deemonoise/D-TRK/docs/plans/2026-10-09-clamps-v2.md

# Клэмпы v2 — план реализации

> **For Claude:** REQUIRED SUB-SKILL: Use superpowers:executing-plans to implement this plan task-by-task.

**Goal:** 4 лапки, прижимающие модуль за угловые бобышки, на существующих стойках верха.

**Architecture:** Новый `module clamp2(dx, dy)` в `enclosure/case.scad`: hull винта и бобышки,
площадка `foam_t` и штырёк в отверстие бобышки. `part = "clamp2"` — 4 лапки на столе,
assembly показывает лапки. Коммиты не делать (правило пользователя).

**Tech Stack:** OpenSCAD 2021.01 (`/Applications/OpenSCAD-2021.01.app/Contents/MacOS/OpenSCAD`).

---

### Task 1: Переменные бобышек

**Files:** Modify: `enclosure/case.scad` (блок «Замерить перед печатью», «Производные»)

Добавить после `clamp_dx`:
```
// Бобышки на задней стороне модуля (клэмпы v2)
boss_x0 = 6.52;    // центр от левого края модуля
boss_x1 = 10.34;   // центр от правого края (сторона Type-C модуля)
boss_y  = 4.3;     // центр от длинных краёв
boss_d  = 6.0;     // наружный диаметр (не замерен)
boss_hole = 2.5;   // отверстие (не замерено)
boss_flip = false; // true — Type-C модуля слева
pin_d = 2.0; pin_h = 1.5;   // штырёк лапки в отверстие бобышки
```
В «Производные» после `clamp_ys`:
```
boss_xs = [mod_x0 + mod_clr + (boss_flip ? boss_x1 : boss_x0),
           mod_x1 - mod_clr - (boss_flip ? boss_x0 : boss_x1)];
boss_ys = [mod_y0 + mod_clr + boss_y, mod_y1 - mod_clr - boss_y];
```

### Task 2: module clamp2 и part

**Files:** Modify: `enclosure/case.scad` (после `module clamp`, assembly, выбор part)

```
// ---------- Лапка v2: винт на стойке, площадка со штырьком на бобышке ----------
// (dx, dy) — смещение центра бобышки от винта
module clamp2(dx, dy) {
    difference() {
        union() {
            hull() {
                cylinder(r = post_r, h = clamp_t);
                translate([dx, dy, 0]) cylinder(d = boss_d, h = clamp_t);
            }
            translate([dx, dy, clamp_t - 0.01]) {
                cylinder(d = boss_d, h = foam_t + 0.01);
                cylinder(d = pin_d, h = foam_t + pin_h + 0.01);
            }
        }
        translate([0, 0, -1]) cylinder(d = screw_d, h = clamp_t + 2);
    }
}
function clamp2_off(i, j) = [boss_xs[i] - clamp_xs[i], boss_ys[j] - clamp_ys[j]];
```
Assembly: заменить строку старых планок на
```
for (i = [0, 1], j = [0, 1]) color("orange")
    translate([clamp_xs[i], clamp_ys[j], clamp_zt - clamp_t])
        clamp2(clamp2_off(i, j)[0], clamp2_off(i, j)[1]);
```
Выбор part: `else if (part == "clamp2") for (i = [0, 1], j = [0, 1]) translate([i*25, j*30, 0]) clamp2(clamp2_off(i, j)[0], clamp2_off(i, j)[1]);`
Шапку файла дополнить `"clamp2"`.

### Task 3: Проверка рендера

Run: `$OS -o /tmp/a.stl -D 'part="clamp2"' case.scad` и `$OS -o /tmp/b.png -D 'part="assembly"' case.scad`
Expected: без WARNING/ERROR, 4 лапки, площадки упираются в низ модуля, лапки не задевают стенки и аккумулятор.
Проверить зазор: `intersection(){ лапки без штырька; модуль }` пусто.

### Task 4: STL и README

- `$OS -o stl/clamp2.stl -D 'part="clamp2"' case.scad`
- `enclosure/README.md`, `README_ru.md`: таблица печати `stl/clamp2.stl` — 1 стол (4 лапки), старые планки как v1;
  крепёж — скотч не нужен для v2; шаг сборки — штырьки в отверстия бобышек; команда рендера; переменные `boss_*`.
