deemonoise/D-TRK/docs/plans/2026-10-06-roadmap.md

# Roadmap: 16 tracks, drum track, song & live, sound, mixer & render

Agreed 2026-10-06. Five blocks, each with its own design + plan, executed in separate sessions in
this order. Every block bumps the project file format (new chunks; older files load with defaults;
files written by a newer block do not open on older firmware).

| # | Block | Design | Plan | Depends on | Status |
|---|---|---|---|---|---|
| 1 | 16 tracks (A/B halves follow the cursor, 8 buttons on the visible half, undo depth 8) | `2026-10-06-16-tracks-design.md` | `2026-10-06-16-tracks.md` | SYNTH / wavetable work landed (`model.h`) | ✅ done 2026-10-06 (checked on the device) |
| 2 | Drum track: KIT instrument (8 lanes, each its own sample by default, optionally an instrument ref), lane mask in `Step::vel`, x-ox views, `ACC` fx | `2026-10-06-kit-drum-track-design.md` | `2026-10-06-kit-drum-track.md` | 1 | ✅ done 2026-10-06 (checked on the device) |
| 3 | Song + live: chain transpose / repeat / scene (`CHN2`), per-track length (`TLEN`), fill (`FIL` / `NFL`, Shift+Play), mute scenes (`SCNS`), live record, punch-in fx (PERF) | `2026-10-06-song-live-design.md` | `2026-10-06-song-live.md` | 1, 2 (drum tracks skip transpose) || ✅ done 2026-10-06 (checked on the device) |
| 4 | Sound: drive (`DRV`), reverb send (`RVB`), master compressor + sidechain, `ARM` arp modes, ARP over CHD, velocity → cutoff / decay | `2026-10-06-sound-fx-design.md` | `2026-10-06-sound-fx.md` | SYNTH / wavetable work landed; 1–3 for track numbers || ✅ done 2026-10-06 (checked on the device) |
| 5 | MIXER view (now its own MIX tab) + offline render: Render WAV (FILE), Resample track / pattern into a project sample (GRID) | `2026-10-06-mixer-render-design.md` | `2026-10-06-mixer-render.md` | 1–4 (render includes delay / reverb / comp) || ✅ done 2026-10-06 (checked on the device) |

Block 1 landed 2026-10-06 and was checked on the device.

Block 2 progress 2026-10-06: tasks 1–5 (model, `ACC`, `KITS` chunk, rename, `expandDrum`) landed, 733
native tests, wt32 builds. Follow-up found in review (resolved with tasks 6–11, see below): the used-sample scan in
`lib/core/src/sample_set.cpp` (`UsedKeys`, ~line 235) and any other "is this sample referenced" site
(bank eviction, project save WAV list, FILE → SAMPLES "in use") must also count `kit[k].sample` of KIT
instruments — do it with task 6 or as its own step before task 11. Also for task 10: add `Kit` cases to
`preset_paths.cpp` `presetTypeName` / `presetRoot` and a `static_assert` on `kTypeNames[]` in
`inst_screen.cpp`.

Block 2, tasks 6–11 (2026-10-06): synth lanes (`Voice::lane` / `laneInst`, `instrOf`, `allocVoice(...,
polyMax)`), Euclid lane, Transpose skips drum tracks, MIDI import onto lanes, GRID mask / lane pad /
track buttons, Euclid dialog `Lane`, INST KIT pages (MAIN + LANES), no KIT presets (`presetTypeHas`),
import dialog `T5*`, README + manual. The used-sample follow-up: `UsedKeys` works from the project
sample list, so lanes were already covered; FILE → SAMPLES Delete now asks through
`projSampleUser`, which counts KIT sampler lanes. 747 native tests pass (run with g++ and a Unity
shim: the PlatformIO registry was not reachable in that session); the UI was type-checked against
host stubs only — `pio run -e wt32` still to run. `Voice` grew by `sizeof(Instrument)` (358 B on
the host), ~5.7 KB for 16 voices: check the boot heap log.

Block 3 (2026-10-06): chain items with transpose / passes / scene (`CHN2`), per-track length
(`TLEN`, `Pattern::trackLen`), mute scenes (`SCNS`, BANK tiles), fill (`CND FIL / NFL`, Shift + Play
held), REC and PERF on the track buttons (`PlayRelease` / `TrackRelease` events, `Cmd::Fill / PerfOn /
PerfOff`, `Status::fill / stepT / stepUs`). 772 native tests pass (g++ + a Unity shim, the PlatformIO
registry still unreachable); UI, engine and trackio type-checked against host stubs only. Choices
beyond the plan: an out-of-range scene in `CHN2` loads as none; deleting the playing chain item
advances at the pass end; REC on a drum track toggles lanes; PERF Fade on a MIDI track halves the
velocity; tapping a track name in REC selects the track instead of muting. To verify on the device:
`pio run -e wt32`, button release timing (fill, PERF), REC landing on the right step, BANK row fields
and scene tiles, the GRID loop line of a short track.

Block 4 (2026-10-06): `Drive` (tanh table, per voice before the filter, lock `DRV`, LFO `DRIVE`),
`Reverb` (Freeverb-lite, 23 KB float buffer in PSRAM, send per instrument, lock `RVB`, idles once its
tail dies out), `Compressor` (master, sidechain bus of `scTrack`), `ARM` modes / rate and ARP + CHD
(`kSynthArpChord`, chord computed at note-on from the played note), velocity -> cutoff / DECAY.
Formats: FMIN bytes 10..13, AUDI 13 bytes, presets v4. 807 native tests pass (g++ + Unity shim);
UI type-checked against host stubs. Choices beyond the plan: ARM DOWN starts from the top note;
makeup gain = threshold drop / 4 (design text) not / 2 (plan code); KIT sampler lanes take the kit's
Rvb send; KIT MAIN page shows Rvb send. To do on the device: `pio run -e wt32`, the CPU bench
(`pio run -e wt32-fxbench`, numbers into the design doc), listening.

Block 5 (2026-10-06): `mt::OfflineRender` (own sequencer on a virtual block clock, live synth,
analytic length, only note-offs after the end, deterministic seed), `Sequencer::setTrackMask`,
`storage::renderWav` / `resample`, `audio::Paused` / `liveSynth`, `audio::cacheWrite` (bank write from
generated data, `finishImport` shared with WAV import), FILE `Render WAV...`, GRID `Resample track /
pattern`, TRACK MIXER view (MAIN = master volume, gone from PROJ), hold a track button + turn =
volume. 823 native tests pass (g++ + Unity shim); UI, render_io, bank, storage type-checked against
host stubs. Choices beyond the plan: renders go to `/samples/render/<project>_P01.wav` / `_SONG.wav`
(Save cleans unknown WAVs out of the project folder, and the Wi-Fi page lists /samples); after the
end only note-offs / releases pass (not controls or synth fx of the next pass); the render guard also
restores track mutes (chain scenes); cancel = long encoder press or Play; MIXER Shift + turn runs
strips 1-8, MAIN, 9-16. Block 4 still waits for its device check (CPU bench numbers).

After the blocks (2026-10-06, from device feedback):
- Step arp `ARS` (fx, INT and MIDI): the sequencer plays the arp as real notes on the following
  steps without a note, every 1..8 steps, ARM orders, 1..4 octaves (`U12` = up, every step, 2
  octaves); notes = CHD chord, else ARP 0/x/y, else the root over at least 2 octaves; stops on a
  note step, OFF, a pattern change, stop. The fast synth ARP / ARM stay as they were.
- Fx command order grouped by meaning in GRID (`fxNextCmd` table; the enum / file format is
  unchanged): notes and arp, timing, chance, pitch and level, sound locks, sample, sends, MIDI only.
- MIDI import: no second project copy (the confirmation runs `importPlan`, the commit imports
  straight into the live project under the lock); the note buffer follows the file size. Fixes NO
  MEMORY on confirm.
- SD: WAV data clamped to the file size (cut files no longer read past the end); `hw::sdRecover`
  remounts only when the card stops answering; `sdBegin` retries with a bus reset. Fixes the card
  being lost until reboot after a sample import / preview error.
- MIXER became the MIX tab of the bottom bar (seven tabs); the Shift + tap / Shift + click / menu
  toggles are gone.

Feature batch (2026-10-06, after the review fixes): restart log + firmware version (crashlog.txt,
PROJ -> SYS), stem export (Render WAV -> STEMS), autosave slot (.auto) + Restore + safe boot (Shift at
power-on), project templates (FILE -> New, /templates), CND PRE / NEI, RAT ramps, groove templates per
pattern + humanize per track (GROV chunk), BIT / SRR lo-fi locks, master DJ filter (AUDI byte 13), PERF
buttons per project (PROJ -> PERF, PRFM chunk), 4 LFOs per instrument with tempo sync (LFOX chunk,
presets v5), FILE sections as page tabs, Wi-Fi page with tabs and scrolling lists.
GRID Fill (Polyend-style) done: `lib/core/src/fill.{h,cpp}` (EVERY N / EUCLID / RANDOM %; NOTE, VEL or an FX slot; CONST / RAMP / RANDOM, notes in the scale; OVERWRITE / EMPTY / NOTES ONLY), `src/ui/fill_dialog` replaces the Euclid dialog (selection or the track up to its length). Euclid core keeps only `euclid()`.

Status 2026-10-07: every block is ✅ — built (`pio run -e wt32`), flashed and checked on the device,
including the feature batch, GRID Fill, the CPU work (voice control in IRAM, math caches, reverb buffer
in internal RAM: ~31 % instead of ~60 % on the heaviest test project), the CPU profile (PROJ -> SYS),
the MIX tab (scope, master on the encoder, A / B, level meters while MIX is shown), page tabs like
FILE on TRACK / PROJ / INST, Bit crush / Downsample in the instrument, the 145-preset factory library
and the SYNTH level fix. Nothing open on this roadmap.

Rules for every session: no commits unless asked; run `pio test -e native` and `pio run -e wt32`
at the end of each task; do not stop for hardware checks — finish the plan, then summarize what to
verify on the device.

Dropped / deferred ideas (see the discussion of 2026-10-06): more than 16 patterns (chain transpose
covers it), song loop points, USB-MIDI device, SMF export, LSDJ-style tables, pan (mono output).
