deemonoise/D-TRK/docs/plans/2026-10-06-16-tracks.md

# 16 Tracks Implementation Plan

> **For Claude:** REQUIRED SUB-SKILL: Use superpowers:executing-plans to implement this plan task-by-task.

**Goal:** Raise the track count from 8 to 16; old project files still load; the GRID overview and the 8 track buttons work on the half (1–8 / 9–16) that holds the cursor.

**Architecture:** `kTracks` becomes 16 and everything sized by it follows. The PATN reader infers the file's track count from the chunk size instead of assuming `kTracks`. The "half" is not state: it is `curTrack / 8`, so moving the cursor is the only way to switch it. Activity / LED masks widen to 16 bits in the core and the engine; the LED mask for the 8 physical LEDs is cut out of the half that holds the selected track.

**Tech Stack:** C++17, PlatformIO (`pio test -e native` for the core, `pio run -e wt32` for the firmware), Unity tests. Design: `docs/plans/2026-10-06-16-tracks-design.md`.

**Rules for this project:** no commits (the user commits); do not stop for hardware checks — finish all tasks, then summarize. Another agent is working in `lib/core/src/synth_syn*`, `wt_*`, `inst_screen.cpp` (SYNTH / wavetable): do not touch those files; if `model.h` has merge noise, keep both changes.

---

### Task 1: `kTracks = 16` in the model

**Files:**
- Modify: `lib/core/src/model.h:6`
- Modify: `src/ui/grid_screen.h:93`
- Modify: `src/audio/audio.cpp:319-321`
- Test: `test/test_model/test_main.cpp`

**Step 1: Write the failing test**

Append to `test/test_model/test_main.cpp` (register with `RUN_TEST` next to the other model tests):

```cpp
void test_sixteen_tracks_defaults() {
  Project p;
  TEST_ASSERT_EQUAL(16, kTracks);
  for (int i = 0; i < kTracks; ++i) {
    TEST_ASSERT_EQUAL(i, p.tracks[i].channel);
    TEST_ASSERT_EQUAL(i, p.tracks[i].instr);
    char nm[9];
    snprintf(nm, sizeof(nm), "TRK%d", i + 1);
    TEST_ASSERT_EQUAL_STRING(nm, p.tracks[i].name);
  }
  TEST_ASSERT_EQUAL(16, kInstruments);  // one instrument per track
}
```

**Step 2: Run it**

Run: `pio test -e native -f test_model`
Expected: FAIL (`Expected 16 Was 8`).

**Step 3: Implement**

`lib/core/src/model.h:6`: `constexpr int kTracks = 16;`

`src/ui/grid_screen.h:93` — the initializer lists 8 values; make it independent of the count:

```cpp
  uint8_t lastNote_[mt::kTracks];  // set to 60 in the constructor
```

and in the constructor (`grid_screen.h:13`):

```cpp
  explicit GridScreen(App& app) : app_(app) { for (uint8_t& n : lastNote_) n = 60; }
```

`src/audio/audio.cpp:319-321` (`AUDIO_BENCH_DRUM` only): the table has 8 entries for `kTracks` slots. Size it by its own length and wrap:

```cpp
  static const DrumMachine kMachines[] = {DrumMachine::Bd8, DrumMachine::Sd8, DrumMachine::Hh8,
                                          DrumMachine::Cy9, DrumMachine::Cp8, DrumMachine::Cb8,
                                          DrumMachine::Tom9, DrumMachine::Hh9};
  constexpr int kBenchTracks = 8;  // instruments kBenchDrumInstr..15
  for (int t = 0; t < kBenchTracks; ++t) {
    ...
    mt::drumSetMachine(d, static_cast<uint8_t>(kMachines[t % 8]));
```

(`benchDrumHits` likewise loops `kBenchTracks`; instruments 8..15 are only 8.)

**Step 4: Run the model test and the whole native suite**

Run: `pio test -e native -f test_model` → PASS.
Run: `pio test -e native` → note every failing test: they are the 8-track assumptions fixed in Tasks 2–4. Do not fix them blindly here.

---

### Task 2: PATN reader infers the file's track count

**Files:**
- Modify: `lib/core/src/project_io.cpp:234-262` (`readPatn`)
- Test: `test/test_project_io/test_main.cpp`

**Step 1: Write the failing tests**

In `test/test_project_io/test_main.cpp` the helper `patn()` (line 451) writes `kTracks` tracks of 6-byte steps. Give it the track count and the step size:

```cpp
// A PATN body: `tracks` tracks of `stepBytes`-byte steps (6 = the 2-slot format, 14 = current).
static std::vector<uint8_t> patn(uint8_t idx, uint8_t len, int extraBytes = 0, int tracks = kTracks,
                                 int stepBytes = 6) {
  std::vector<uint8_t> p = {idx, len, static_cast<uint8_t>(Resolution::Eighth), 60};
  for (int t = 0; t < tracks; ++t)
    for (int s = 0; s < len; ++s) {
      std::vector<uint8_t> st(stepBytes, 0);
      st[0] = static_cast<uint8_t>((t + s) % 128);
      st[1] = 100;
      p.insert(p.end(), st.begin(), st.end());
    }
  if (extraBytes > 0) p.resize(p.size() + extraBytes, 0);
  if (extraBytes < 0) p.resize(p.size() + extraBytes);
  return p;
}
```

Add tests:

```cpp
// Files from the 8-track firmware: tracks 1-8 load, 9-16 stay clear. Both step formats.
void test_patn_eight_tracks_loads() {
  for (int stepBytes : {6, 14}) {
    std::vector<uint8_t> f = fileHeader();
    putChunk(f, "PATN", patn(3, 16, 0, 8, stepBytes));
    finish(f);
    TEST_ASSERT_EQUAL(static_cast<int>(LoadErr::Ok), static_cast<int>(loadBytes(f)));
    const Pattern& pt = b.patterns[3];
    TEST_ASSERT_EQUAL(16, pt.length);
    TEST_ASSERT_EQUAL((7 + 15) % 128, pt.steps[7][15].note);
    for (int t = 8; t < kTracks; ++t)
      for (int s = 0; s < 16; ++s) TEST_ASSERT_TRUE(pt.steps[t][s].isEmpty());
  }
}

void test_patn_sixteen_tracks_round_trip() {
  a.reset();
  a.patterns[5].length = 24;
  a.patterns[5].steps[15][23].note = 71;
  a.patterns[5].steps[8][0].fx[5] = {Fx::DLY, 99};
  VecSink out;
  TEST_ASSERT_TRUE(saveProject(a, out));
  VecSource in(out.data);
  TEST_ASSERT_EQUAL(static_cast<int>(LoadErr::Ok), static_cast<int>(loadProject(in, b)));
  TEST_ASSERT_EQUAL(71, b.patterns[5].steps[15][23].note);
  TEST_ASSERT_EQUAL(static_cast<int>(Fx::DLY), static_cast<int>(b.patterns[5].steps[8][0].fx[5].cmd));
  TEST_ASSERT_EQUAL(99, b.patterns[5].steps[8][0].fx[5].val);
}
```

(`VecSink` / `VecSource`: use whatever the file's `test_round_trip_full_project` uses — copy its pattern.)

`test_patn_size_mismatch` must still pass: an 8-track 6-byte body ± 1 byte and + 6 bytes match none of the four (tracks, step) combinations. Keep `test_trks_count_not_eight` as is: the `trks(10, 10)` case now loads 10 tracks (count ≤ kTracks); update its assertions: `b.tracks[9].name == "K9"`, and tracks 10–15 keep the defaults.

**Step 2: Run them**

Run: `pio test -e native -f test_project_io`
Expected: `test_patn_eight_tracks_loads` FAILS (`BadValue`), the round trip passes already.

**Step 3: Implement**

Replace the step-size inference in `readPatn` (`project_io.cpp:239-246`) and the fill loop:

```cpp
  const int len = h[1];
  // Track count and step size from the body size: 16 or 8 tracks (files of the 8-track firmware)
  // x 14-byte (6 slots) or 6-byte (2 slots, older) steps. The four products differ for any length.
  const uint32_t body = size - kPatHeader;
  int tracks = 0;
  uint32_t stepBytes = 0;
  for (int tr : {kTracks, 8})
    for (uint32_t sb : {static_cast<uint32_t>(sizeof(Step)), kOldStepBytes})
      if (!stepBytes && len && body == static_cast<uint32_t>(tr) * len * sb) {
        tracks = tr;
        stepBytes = sb;
      }
  if (!stepBytes && body != 0) return LoadErr::BadValue;
```

and `for (int t = 0; t < tracks; ++t)` in the step loop (`pt.clear()` already zeroes the rest). Keep the `len == 0` behaviour: `body == 0` → an empty pattern of `kMinSteps`.

**Step 4: Run**

Run: `pio test -e native -f test_project_io` → all PASS.

---

### Task 3: 16-bit activity for the LEDs, half-aware LED mask

**Files:**
- Modify: `lib/core/src/sequencer.h:86-91,182`, `lib/core/src/sequencer.cpp:624`
- Modify: `src/engine/engine.h:39`, `src/engine/engine.cpp:31,72-74,134`
- Modify: `lib/core/src/track_leds.h`
- Modify: `src/ui/app.cpp:206-214`, `src/ui/app.h:133` (unchanged size, keep)
- Test: `test/test_track_leds/test_main.cpp`

**Step 1: Write the failing test**

```cpp
// 16 tracks, 8 LEDs: the LEDs show the half (tracks 1-8 or 9-16) that holds the selected track.
void test_half_mask_follows_selected() {
  // selected 11 (half B, LED 3), track 9 flashing (LED 1), track 2 flashing (half A, hidden)
  TEST_ASSERT_EQUAL_HEX8((1 << 3) | (1 << 1), trackLedMaskHalf(11, (1u << 9) | (1u << 2)));
  // selected 2 (half A): track 9 hidden, track 2 flashing goes dark
  TEST_ASSERT_EQUAL_HEX8(0, trackLedMaskHalf(2, (1u << 9) | (1u << 2)));
  TEST_ASSERT_EQUAL_HEX8(1 << 7, trackLedMaskHalf(15, 0));
  TEST_ASSERT_EQUAL_HEX8(0, trackLedMaskHalf(-1, 1u << 9));  // nothing selected: half A
}
```

Register it in `main()`.

**Step 2: Run** `pio test -e native -f test_track_leds` → FAIL (no `trackLedMaskHalf`).

**Step 3: Implement**

`track_leds.h`, after `trackLedMask`:

```cpp
// 16 tracks on 8 LEDs: the half (tracks 0-7 or 8-15) holding the selected track; flash bit = track.
inline uint8_t trackLedMaskHalf(int selected, uint16_t flash) {
  const int half = selected >= 8 && selected < 16 ? 1 : 0;
  const uint8_t f = static_cast<uint8_t>(flash >> (half * 8));
  return trackLedMask(selected >= 0 ? selected - half * 8 : -1, f);
}
```

Widen the activity path to `uint16_t`:

- `sequencer.h`: `uint16_t takeActivity() { const uint16_t a = activity_; ... }`, `uint16_t activity_ = 0;`
- `sequencer.cpp:624`: `activity_ |= static_cast<uint16_t>(1u << e.track);`
- `engine.cpp:31`: `std::atomic<uint16_t> activity{0};`; line 72: `const uint16_t act = ...`; line 134 and `engine.h:39`: `uint16_t takeActivity()`.
- `app.cpp` `updateLeds`:

```cpp
void App::updateLeds(uint32_t now) {
  const uint16_t act = engine::takeActivity();
  uint16_t flash = 0;
  for (int i = 0; i < mt::kTracks; ++i) {
    if (act & (1u << i)) flashUntil_[i] = now + kFlashMs;
    if (static_cast<int32_t>(flashUntil_[i] - now) > 0) flash |= static_cast<uint16_t>(1u << i);
  }
  hw::trackLeds(mt::trackLedMaskHalf(curTrack_, flash));
}
```

**Step 4: Run** `pio test -e native -f test_track_leds` → PASS. `pio test -e native -f test_sequencer` → PASS (activity type only).

---

### Task 4: Core tests at the new bounds (edit ops, Euclid, sequencer, MIDI import)

**Files:**
- Modify: `lib/core/src/midi_import.h:11` (comment `0..7` → `0..kTracks-1`), `lib/core/src/edit_ops.h:20` (comment)
- Test: `test/test_edit/test_main.cpp`, `test/test_euclid/test_main.cpp`, `test/test_sequencer/test_main.cpp`, `test/test_import/test_main.cpp`

**Step 1: Add tests** (copy the style of the neighbouring tests in each file; names below):

- `test_edit`: `test_paste_clipped_at_track_16` — a 3-track clipboard pasted at track 14 writes tracks 14, 15 and drops the third; `test_selection_spans_halves` — `Sel` from track 5 to 10 (both orders) normalizes to t0 = 5, t1 = 10 and `clearSel` clears exactly those tracks.
- `test_euclid`: `test_euclid_track_15` — apply to track 15 with hits 4 / steps 16, four notes on that track, track 14 untouched.
- `test_sequencer`: `test_track_15_plays` — a note on track 15 at step 0 produces a NoteOn on channel `tracks[15].channel` (MIDI out) and `takeActivity()` has bit 15.
- `test_import`: `test_twelve_channels_to_twelve_tracks` — an SMF with notes on channels 1–12 (one source each) imported with the default map lands on tracks 0–11; track 11 holds the channel-12 note.

**Step 2: Run** `pio test -e native` → the new tests FAIL only if a bound is still 8 somewhere; expected: PASS straight away for edit / euclid / sequencer (they are `kTracks`-bounded), PASS for import.

If a test fails, the failing spot is a literal 8 — fix it in the core file, not the test.

**Step 3: Run the whole suite** `pio test -e native` → every test PASS.

---

### Task 5: GRID overview shows the cursor's half

**Files:**
- Modify: `src/ui/grid_screen.h` (add `half()`, `kOverviewTracks`)
- Modify: `src/ui/grid_screen.cpp:273-300` (`trackKey`, `hit`), `:336-345` (name tap), `:608-656` (`drawOverview`)

**Step 1: Helpers** in `grid_screen.h`, private:

```cpp
  static constexpr int kOverviewTracks = 8;                     // columns per half
  int half() const { return track() / kOverviewTracks; }         // 0 = tracks 1-8, 1 = 9-16
  int firstTrack() const { return half() * kOverviewTracks; }
```

**Step 2: `drawOverview`** — both loops over tracks become columns:

```cpp
  for (int col = 0; col < kOverviewTracks; ++col) {
    const int tr = firstTrack() + col;
    const mt::TrackCfg& t = p.tracks[tr];
    s.setTextColor(t.solo ? kCursor : (p.trackAudible(tr) ? kText : kDim));
    s.drawString(t.name, kNumW + col * kColW + 4, gridY - kNamesH);
  }
```

and in the row loop `for (int col ...) { const int tr = firstTrack() + col; const int x = kNumW + col * kColW; ... }` — every `pt.steps[tr]`, `p.tracks[tr]`, `selected(tr, step)`, `tr == track()` keeps the absolute `tr`; only `x` uses `col`.

Half indicator: in the step-number column header (top-left, `x = 2`, where Detail prints `T%d`) draw `"A"` or `"B"` in `kDim` when `!detail_`:

```cpp
  s.setTextColor(kDim);
  s.drawString(half() ? "9-16" : "1-8", 2, gridY - kNamesH);
```

(`kNumW` = 32 px: "1-8" / "9-16" fit in the default 6-px font; check on the device, fall back to "A" / "B" if not.)

**Step 3: `hit`** (overview branch):

```cpp
  if (!detail_) {
    const int col = (x - kNumW) / kColW;
    if (col >= kOverviewTracks) return false;
    tr = firstTrack() + col;
    field = kNote;
    return true;
  }
```

**Step 4: Name tap** (`:339-340`):

```cpp
    const int col = (ev.x - kNumW) / kColW;
    if (!detail_ && col >= kOverviewTracks) return;
    const int tr = detail_ ? track() : firstTrack() + col;
```

**Step 5: `trackKey`** — button N selects track N of the visible half; note entry keeps the button index:

```cpp
  if (shift) return false;
  app_.setCurTrack(firstTrack() + n);
```

(`enterDegree(n, shift)` above it stays: degrees are button numbers.)

**Step 6: `moveTrack` / `moveField`** need no change: `setCurTrack` wraps at 16, `half()` follows. `cursorMoved()` already requests a redraw.

**Step 7: Build** `pio run -e wt32` → compiles.

---

### Task 6: App maps the 8 buttons onto the visible half

**Files:**
- Modify: `src/ui/app.cpp:188-204` (`trackKey`)

**Step 1: Implement**

```cpp
// Button n (0-7) addresses track n of the half holding the cursor (1-8 or 9-16). Grid takes
// selection and note entry, the sample editor plays slices (button index); Shift + N mutes on
// every other screen too.
void App::trackKey(int n, bool shift) {
  if (n < 0 || n >= 8) return;
  const int track = (curTrack_ / 8) * 8 + n;
  if (tab_ == Tab::Grid && grid_.trackKey(n, shift)) return;
  if (tab_ == Tab::Inst && inst_.trackKey(n, shift)) return;
  if (!shift) {
    setCurTrack(track);
    return;
  }
  mt::TrackCfg& t = p_->tracks[track];
  ... (mute toggle as now, toast "TRACK %d" with track + 1)
```

**Step 2: Build** `pio run -e wt32` → compiles.

---

### Task 7: Undo depth and PSRAM budget

**Files:**
- Modify: `lib/core/src/undo.h:10`
- Check: `src/main.cpp`, `src/ui/app.cpp:17-19`

**Step 1:** `static constexpr int kDepth = 8;` (8 x 28 KB ≈ 230 KB; the project ≈ 460 KB).

**Step 2:** Make sure the boot log prints the free PSRAM after the project and undo buffers are allocated. If `main.cpp` does not log it, add after the undo allocation:

```cpp
  Serial.printf("psram free %u KB\n", heap_caps_get_free_size(MALLOC_CAP_SPIRAM) / 1024);
```

**Step 3:** `pio run -e wt32` → compiles. (The number itself is read off the device later; if it is below ~300 KB, drop `kDepth` to 4 and say so in the summary. Any undo test that asserts the depth 32 (`test_util` or `test_edit`): change the constant in the test to `Undo::kDepth`.)

---

### Task 8: Sweep for literal eights and 8-track text

**Files:** `src/ui/*.cpp`, `src/ui/*.h`, `lib/core/src/*.h`, `lib/core/src/*.cpp` (except the SYNTH / wavetable files listed at the top)

**Step 1:** `grep -n '\b8\b' src/ui/*.cpp src/ui/app.h lib/core/src/edit_ops.* lib/core/src/midi_import.* lib/core/src/euclid.* lib/core/src/sequencer.*` and read each hit: anything meaning "track count" becomes `kTracks` / `kOverviewTracks`; bit widths of `kFxSlots`, hex nibbles, `kLocks` etc. stay.

Known spots: `edit_ops.h:20` comment; `midi_import.h:11` comment; `track_leds.h:8` (`trackLedMask` keeps 8: it is the LED count); manual / README text (Task 9).

**Step 2:** Status bar: find where the current track is printed (`grep -n 'curTrack' src/ui/app.cpp src/ui/*.cpp`) and make sure two digits fit the field (`T16`); widen the field by one glyph if it clips.

**Step 3:** `pio test -e native` → all PASS; `pio run -e wt32` → compiles.

---

### Task 9: Docs

**Files:**
- Modify: `README.md:3` ("8-дорожечный" → "16-дорожечный"), the track-button sections (`README.md:34-59`)
- Modify: `docs/manual.html` — GRID Overview, "Кнопки дорожек", status bar

**Step 1:** README: 16 tracks in the intro; in "Кнопки дорожек": кнопка N — дорожка N видимой половины (1–8 или 9–16), половину выбирает курсор; Shift+N — mute той же дорожки; LED — та же половина.

**Step 2:** manual: Overview shows 8 of the 16 tracks, the header shows `1-8` / `9-16`, moving the cursor past the 8th track (encoder with Shift, track-name tap in Detail, track button) switches the half; Paste limit "8-я дорожка" → "16-я"; the track buttons section as in the README; mention that files written by this version do not open on older firmware.

**Step 3:** Final: `pio test -e native` → all PASS, `pio run -e wt32` → compiles. Report the free-PSRAM line (if the device was flashed) and the undo depth chosen.
