deemonoise/D-TRK/docs/plans/2026-10-06-song-live.md

# Song + Live Implementation Plan

> **For Claude:** REQUIRED SUB-SKILL: Use superpowers:executing-plans to implement this plan task-by-task.

**Goal:** Chain items with transpose / repeat / scene, per-track pattern length, fill, mute scenes, live recording and punch-in effects from the track buttons.

**Architecture:** The sequencer expands a *working copy* of each step (`adjustStep`: chain transpose, perf fx slot) and indexes it through the track's own length; CND gets two held-button conditions; chain items get three parallel arrays saved in a new chunk; the UI adds fields to the BANK chain rows, scene tiles, `Rec` / `Perf` modes in GRID and a `Pat len` param in TRACK. Design: `docs/plans/2026-10-06-song-live-design.md`.

**Tech Stack:** C++17, PlatformIO (`pio test -e native -f <test>`, `pio run -e wt32`), Unity.

**Rules:** no commits (the user commits). Do not stop for hardware checks; finish, then summarize. Do not touch `lib/core/src/synth_syn*`, `wt_*`, `src/ui/inst_screen.cpp` (another agent's SYNTH / wavetable work). Blocks 1 (16 tracks) and 2 (drum track, `Project::trackIsDrum(t)`) are done; if `trackIsDrum` does not exist yet, add `bool trackIsDrum(int) const { return false; }` to `Project` with a `// block 2` comment.

Part A = Tasks 1–5 (song), Part B = Tasks 6–11 (live). Each task ends with the whole native suite green and `pio run -e wt32` compiling.

---

## Part A — Song

### Task 1: Chain arrays + `CHN2` chunk

**Files:**
- Modify: `lib/core/src/model.h` (`Project`), `lib/core/src/model.cpp` (`reset`)
- Modify: `lib/core/src/project_io.cpp` (reader dispatch `:433-446`, writer after `PROJ` `:302`)
- Test: `test/test_project_io/test_main.cpp`

**Step 1: Failing tests**

```cpp
void test_chn2_round_trip() {
  a.reset();
  a.chainLen = 3;
  a.chain[0] = 2; a.chainTr[0] = -5; a.chainRep[0] = 4; a.chainScene[0] = 3;
  a.chain[2] = 7; a.chainTr[2] = 12; a.chainRep[2] = 1;
  VecSink out;  // as in test_round_trip_full_project
  TEST_ASSERT_TRUE(saveProject(a, out));
  VecSource in(out.data);
  TEST_ASSERT_EQUAL(static_cast<int>(LoadErr::Ok), static_cast<int>(loadProject(in, b)));
  TEST_ASSERT_EQUAL(-5, b.chainTr[0]);
  TEST_ASSERT_EQUAL(4, b.chainRep[0]);
  TEST_ASSERT_EQUAL(3, b.chainScene[0]);
  TEST_ASSERT_EQUAL(12, b.chainTr[2]);
  TEST_ASSERT_EQUAL(1, b.chainRep[1]);
}

// A file without CHN2 (old firmware): chain from PROJ, tr 0, rep 1, scene 0.
void test_chain_without_chn2_defaults() {
  a.reset();
  a.chainLen = 2; a.chain[1] = 5;
  VecSink out;
  TEST_ASSERT_TRUE(saveProject(a, out));
  std::vector<uint8_t> f = withoutChunks(out.data, {"CHN2"});
  TEST_ASSERT_EQUAL(static_cast<int>(LoadErr::Ok), static_cast<int>(loadBytes(f)));
  TEST_ASSERT_EQUAL(5, b.chain[1]);
  TEST_ASSERT_EQUAL(0, b.chainTr[1]);
  TEST_ASSERT_EQUAL(1, b.chainRep[1]);
  TEST_ASSERT_EQUAL(0, b.chainScene[1]);
}

void test_chn2_garbage_clamped() {
  std::vector<uint8_t> f = fileHeader();
  // count 1: pattern 200, transpose +90, repeat 0, scene 9
  putChunk(f, "CHN2", {1, 200, 90, 0, 9});
  finish(f);
  TEST_ASSERT_EQUAL(static_cast<int>(LoadErr::Ok), static_cast<int>(loadBytes(f)));
  TEST_ASSERT_EQUAL(1, b.chainLen);
  TEST_ASSERT_EQUAL(kPatterns - 1, b.chain[0]);
  TEST_ASSERT_EQUAL(24, b.chainTr[0]);
  TEST_ASSERT_EQUAL(1, b.chainRep[0]);
  TEST_ASSERT_EQUAL(0, b.chainScene[0]);
}
```

(`withoutChunks` exists at `:570`; `CHN2` must be removed *after* `PROJ` is kept, which it is.)

**Step 2:** `pio test -e native -f test_project_io` → FAIL (no `chainTr`).

**Step 3: Implement**

`model.h`, in `Project` after `chainLen`:

```cpp
  // Per chain item: transpose of melodic tracks (semitones), passes before advancing, mute scene
  // recalled when the item starts (0 = none, 1..kScenes). See chainInsert / chainDelete (edit_ops).
  int8_t chainTr[kChainMax] = {0};
  uint8_t chainRep[kChainMax] = {0};  // 1..kChainRepMax; reset() sets 1
  uint8_t chainScene[kChainMax] = {0};
```

and constants near `kChainMax`: `constexpr int kChainRepMax = 16; constexpr int kChainTrMax = 24; constexpr int kScenes = 8;`. `reset()`: `memset(chainTr, 0, ...)`, `chainRep` all 1, `chainScene` 0.

`project_io.cpp`: `constexpr size_t kChn2Rec = 4;`

```cpp
LoadErr readChn2(CrcSource& in, uint32_t size, Project& p) {
  return readRecords(in, size, kChn2Rec, kChainMax, [&](int i, const uint8_t* b) {
    p.chain[i] = clampu(b[0], 0, kPatterns - 1);
    const int tr = static_cast<int8_t>(b[1]);
    p.chainTr[i] = static_cast<int8_t>(tr < -kChainTrMax ? -kChainTrMax : (tr > kChainTrMax ? kChainTrMax : tr));
    p.chainRep[i] = clampu(b[2], 1, kChainRepMax);
    p.chainScene[i] = clampu(b[3], 0, kScenes);
  }, &p.chainLen);  // the count byte also sets chainLen — check readRecords' signature; if it has no
                    // count-out parameter, read the count byte here and call the record loop yourself.
}
```

Writer, right after the `PROJ` chunk: count = `chainLen`, then `chainLen` records `{chain[i], (uint8_t)chainTr[i], chainRep[i], chainScene[i]}`. Dispatch: `else if (memcmp(ch, "CHN2", 4) == 0) e = readChn2(in, size, out);`. `PROJ` keeps writing `chain` / `chainLen` (old firmware reads them).

**Step 4:** `pio test -e native -f test_project_io` → PASS. `pio test -e native` → PASS.

---

### Task 2: Chain insert / delete move all arrays

**Files:**
- Modify: `lib/core/src/edit_ops.h`, `lib/core/src/edit_ops.cpp`
- Modify: `src/ui/bank_screen.cpp:272-304` (`insertRow`, `deleteRow` use the helpers)
- Test: `test/test_edit/test_main.cpp`

**Step 1: Tests**

```cpp
void test_chain_insert_moves_all_fields() {
  Project p;
  p.chainLen = 2;
  p.chain[0] = 1; p.chainTr[0] = 3; p.chainRep[0] = 2; p.chainScene[0] = 1;
  p.chain[1] = 4; p.chainTr[1] = -2; p.chainRep[1] = 5; p.chainScene[1] = 2;
  TEST_ASSERT_TRUE(chainInsert(p, 1, 9));
  TEST_ASSERT_EQUAL(3, p.chainLen);
  TEST_ASSERT_EQUAL(9, p.chain[1]); TEST_ASSERT_EQUAL(0, p.chainTr[1]);
  TEST_ASSERT_EQUAL(1, p.chainRep[1]); TEST_ASSERT_EQUAL(0, p.chainScene[1]);
  TEST_ASSERT_EQUAL(4, p.chain[2]); TEST_ASSERT_EQUAL(-2, p.chainTr[2]);
  TEST_ASSERT_EQUAL(5, p.chainRep[2]); TEST_ASSERT_EQUAL(2, p.chainScene[2]);
  chainDelete(p, 0);
  TEST_ASSERT_EQUAL(2, p.chainLen);
  TEST_ASSERT_EQUAL(9, p.chain[0]);
  TEST_ASSERT_EQUAL(-2, p.chainTr[1]);
}
```

**Step 2:** `pio test -e native -f test_edit` → FAIL.

**Step 3:** `edit_ops.h`:

```cpp
// Chain rows: insert pattern `pat` (tr 0, rep 1, no scene) at `at` (0..chainLen), false when full;
// delete row `at`. Both keep chain / chainTr / chainRep / chainScene aligned.
bool chainInsert(Project& p, int at, uint8_t pat);
void chainDelete(Project& p, int at);
```

Implementation: `memmove` each array by one from `at`; clamp `at` to `0..chainLen`; `chainInsert` returns false when `chainLen >= kChainMax`. `bank_screen.cpp` `insertRow` / `deleteRow`: replace the inline shifting of `p.chain` with the helpers (keep their `postChainEdit` calls and clamping).

**Step 4:** `pio test -e native` → PASS; `pio run -e wt32` → compiles.

---

### Task 3: Sequencer — transpose, repeat, scene

**Files:**
- Modify: `lib/core/src/sequencer.h` (`Sched`, members, `adjustStep`), `lib/core/src/sequencer.cpp` (`start` `:45-60`, `scheduleStep` `:370-380`, `skipStep` `:492`, `endOfPass` `:508`, `rewind` `:273-286`, `chainEdited`)
- Test: `test/test_sequencer/test_main.cpp`

**Step 1: Tests** (fixture: `p`, `seq`, `sink`, `run`; MIDI tracks; 120 BPM, a 4-step 16th pattern is 500 000 us)

```cpp
void test_chain_transpose_melodic_not_drum() {
  p->songMode = true;
  p->chainLen = 1;
  p->chain[0] = 0;
  p->chainTr[0] = 5;
  p->patterns[0].length = 4;
  p->patterns[0].steps[0][0].note = 60;  // melodic
  p->patterns[0].steps[1][0].note = 36;  // drum track (block 2); without block 2 this assert is skipped
  seq->start(0, *sink);
  run(0, 10000);
  TEST_ASSERT_EQUAL(1, sink->times(0x90, 65).size());
  if (p->trackIsDrum(1)) TEST_ASSERT_EQUAL(1, sink->times(0x91, 36).size());
}

void test_chain_repeat_advances_after_n_passes() {
  p->songMode = true;
  p->chainLen = 2;
  p->chain[0] = 0; p->chainRep[0] = 3;
  p->chain[1] = 1;
  p->patterns[0].length = 4; p->patterns[0].steps[0][0].note = 60;
  p->patterns[1].length = 4; p->patterns[1].steps[0][0].note = 62;
  seq->start(0, *sink);
  run(0, 1510000);  // 3 passes of P0, then P1 starts at 1 500 000
  TEST_ASSERT_EQUAL(3, sink->times(0x90, 60).size());
  auto on62 = sink->times(0x90, 62);
  TEST_ASSERT_EQUAL(1, on62.size());
  TEST_ASSERT_EQUAL(1500000, on62[0]);
}

void test_chain_scene_sets_mutes() {
  p->songMode = true;
  p->chainLen = 1; p->chain[0] = 0; p->chainScene[0] = 2;
  p->scenes[1] = 1u << 3;  // scene 2 mutes track 4
  p->patterns[0].length = 4;
  p->patterns[0].steps[3][0].note = 60;
  seq->start(0, *sink);
  run(0, 10000);
  TEST_ASSERT_TRUE(p->tracks[3].mute);
  TEST_ASSERT_EQUAL(0, sink->times(0x93, 60).size());
}
```

(`Project::scenes` arrives in Task 6; add the field now — `uint16_t scenes[kScenes]`, `reset()` sets `kSceneEmpty = 0xFFFF` — the chunk comes in Task 6.)

**Step 2:** `pio test -e native -f test_sequencer` → FAIL to compile / fail.

**Step 3: Implement**

`sequencer.h`: `Sched` gains `uint8_t rep, prevRep;`; members `uint8_t rep_ = 0;` and:

```cpp
  // The step as it plays: chain transpose on melodic tracks, perf fx (Task 11). Returns the copy.
  void adjustStep(Step& s, int track) const;
  int8_t chainTranspose() const { return songPos_ >= 0 ? p_.chainTr[songPos_] : 0; }
  void applyScene(int songPos, uint64_t t);
```

`sequencer.cpp`:

```cpp
void Sequencer::adjustStep(Step& s, int track) const {
  const int tr = chainTranspose();
  if (tr && s.hasNote() && !p_.trackIsDrum(track)) {
    const int n = s.note + tr;
    s.note = static_cast<uint8_t>(n < 0 ? 0 : (n > 127 ? 127 : n));
  }
}

// Writes the item's mute scene into the tracks; muted tracks go silent at t.
void Sequencer::applyScene(int songPos, uint64_t t) {
  if (songPos < 0 || songPos >= chainLen()) return;
  const uint8_t sc = p_.chainScene[songPos];
  if (sc == 0 || sc > kScenes || p_.scenes[sc - 1] == kSceneEmpty) return;
  const uint16_t m = p_.scenes[sc - 1];
  for (int tr = 0; tr < kTracks; ++tr) {
    const bool mute = (m >> tr) & 1;
    if (mute && !p_.tracks[tr].mute) pushOff(tr, t);
    p_.tracks[tr].mute = mute;
  }
}
```

`scheduleStep` / `skipStep`: `Step s = pat.steps[tr][pos_]; adjustStep(s, tr);` and use `s` where `pat.steps[tr][pos_]` was (the `hasNote` / `kNoteOff` / `expand(s, ...)` calls). Record `h.prevRep = rep_` next to `prevSong`, `h.rep = rep_` next to `h.song`; `rewind` restores `rep_ = h.prevRep`.

`endOfPass`:

```cpp
  if (songActive()) {
    if (++rep_ < clampu(p_.chainRep[songPos_], 1, kChainRepMax)) {
      next = -1;  // another pass of the same item: ties and CND go on
    } else {
      rep_ = 0;
      songPos_ = songPos_ + 1 < chainLen() ? songPos_ + 1 : 0;
      next = chainAt(songPos_);
      applyScene(songPos_, tickTime(stepTick_));
      if (next == cur_) next = -1;
    }
  } else {
    songPos_ = -1;
    rep_ = 0;
  }
```

`start()` (song branch, `:52`): `rep_ = 0; applyScene(0, now);`. `chainEdited()`: after remapping `songPos_`, `if (songPos_ >= 0 && rep_ >= p_.chainRep[songPos_]) rep_ = 0;`. `stop()` / `showStopped()`: `rep_ = 0`.

**Step 4:** `pio test -e native -f test_sequencer` → PASS; whole suite PASS.

---

### Task 4: Per-track length (`trackLen`, `TLEN`, polymeter)

**Files:**
- Modify: `lib/core/src/model.h` (`Pattern`), `lib/core/src/model.cpp` (`Pattern::clear`)
- Modify: `src/storage/storage.cpp:47` (static_assert: `3 + kTracks + sizeof(Step) * ...`)
- Modify: `lib/core/src/project_io.cpp` (`TLEN` read / write after each `PATN`)
- Modify: `lib/core/src/sequencer.cpp` (`scheduleStep`, `skipStep` step index)
- Test: `test/test_project_io/test_main.cpp`, `test/test_sequencer/test_main.cpp`

**Step 1: Tests**

```cpp
// project_io
void test_tlen_round_trip_and_default() {
  a.reset();
  a.patterns[2].steps[0][0].note = 60;  // stored pattern
  a.patterns[2].trackLen[5] = 3;
  VecSink out;
  TEST_ASSERT_TRUE(saveProject(a, out));
  VecSource in(out.data);
  TEST_ASSERT_EQUAL(static_cast<int>(LoadErr::Ok), static_cast<int>(loadProject(in, b)));
  TEST_ASSERT_EQUAL(3, b.patterns[2].trackLen[5]);
  TEST_ASSERT_EQUAL(0, b.patterns[2].trackLen[4]);
  std::vector<uint8_t> f = withoutChunks(out.data, {"TLEN"});
  TEST_ASSERT_EQUAL(static_cast<int>(LoadErr::Ok), static_cast<int>(loadBytes(f)));
  TEST_ASSERT_EQUAL(0, b.patterns[2].trackLen[5]);
}

// sequencer: track 0 has length 3 inside a 16-step pattern: its step 0 plays at positions 0, 3, 6, ...
void test_track_length_polymeter() {
  p->patterns[0].length = 16;
  p->patterns[0].trackLen[0] = 3;
  p->patterns[0].steps[0][0].note = 60;
  p->patterns[0].steps[1][15].note = 62;  // the pattern still has 16 steps
  seq->start(0, *sink);
  run(0, 2010000);  // one pass = 2 000 000 us
  auto on = sink->times(0x90, 60);
  TEST_ASSERT_EQUAL(6, on.size());  // positions 0, 3, 6, 9, 12, 15
  TEST_ASSERT_EQUAL(375000, on[1]);
  TEST_ASSERT_EQUAL(1, sink->times(0x91, 62).size());
}
```

**Step 2:** run both → FAIL.

**Step 3:** `model.h` `Pattern`: `uint8_t trackLen[kTracks];  // 0 = length, else 1..length (polymeter)` after `swing`; `clear()` zeroes it. Static_assert in `storage.cpp` → `3 + mt::kTracks + sizeof(mt::Step) * ...`. `project_io.cpp`: writer, after each `PATN`: `TLEN` chunk `{idx, trackLen[0..15]}` (17 bytes) when any `trackLen` is non-zero; reader `readTlen`: size must be `1 + kTracks` else `BadValue`; idx ≥ kPatterns → skip; values `clampu(b[1+t], 0, pattern.length)`. Dispatch entry `"TLEN"`.

Sequencer, a helper in `sequencer.h`:

```cpp
  static int stepIndex(const Pattern& pt, int track, int pos) {
    const uint8_t n = pt.trackLen[track];
    return n ? pos % n : pos;
  }
```

`scheduleStep` / `skipStep`: `Step s = pat.steps[tr][stepIndex(pat, tr, pos_)];`.

**Step 4:** both tests PASS, suite PASS, `pio run -e wt32` compiles.

---

### Task 5: UI for Part A — BANK chain fields, TRACK `Pat len`, GRID boundary

**Files:**
- Modify: `src/ui/bank_screen.h`, `src/ui/bank_screen.cpp` (`editRow` `:306`, `chainInput` `:341`, `chainTouch` `:363`, `drawChain` `:405`, `openRowMenu` title, `Length` handling in `onMenu`)
- Modify: `src/ui/track_screen.cpp` (param list), `src/ui/grid_screen.cpp` (`drawOverview`, `drawDetail`)

**Step 1 — BANK row fields.** `bank_screen.h`: `enum RowField : uint8_t { kFPat, kFTr, kFRep, kFScene, kFCount }; int rowField_ = kFPat;`. `chainInput`, `EncTurn` in `rowEdit_`: `ev.shift ? rowField_ = clampi(rowField_ + ev.delta, 0, kFCount - 1) : editRow(ev.delta)`. `editRow(delta)` edits the field under the lock then `postChainEdit(row_, ChainOp::Edit)`:

```cpp
  switch (rowField_) {
    case kFPat: v = clampi(p.chain[row_] + delta, 0, mt::kPatterns - 1); p.chain[row_] = v; break;
    case kFTr: p.chainTr[row_] = clampi(p.chainTr[row_] + delta, -mt::kChainTrMax, mt::kChainTrMax); break;
    case kFRep: p.chainRep[row_] = clampi(p.chainRep[row_] + delta, 1, mt::kChainRepMax); break;
    case kFScene: p.chainScene[row_] = clampi(p.chainScene[row_] + delta, 0, mt::kScenes); break;
  }
```

`drawChain` row text: `P05`, then ` +3` / ` -5` when tr ≠ 0, ` x2` when rep > 1, ` S1` when scene ≠ 0; in row edit draw the four fields at fixed x (16, 64, 112, 160) with the active one in `kCursor` and show defaults as `+0 x1 S-` so every field is tappable. `chainTouch`: a tap on a field x-range in the selected row sets `rowField_` (and enters row edit). Title in `openRowMenu`: `SONG 02: P05 +3 x2 S1`.

**Step 2 — scene handling of BANK `Length`.** Where `onMenu` applies the pattern `Length` (find `kLength` or the length menu id), after setting `length`: `for (uint8_t& n : pt.trackLen) if (n > pt.length) n = pt.length;`.

**Step 3 — TRACK `Pat len`.** In `track_screen.cpp`'s param table add after `defGate` (read `track_screen.cpp:20-80` for the `Param` shape):

```cpp
  {"Pat len",
   [this](char* o, int n) {
     const mt::Pattern& pt = app_.project().patterns[app_.editPattern()];
     const uint8_t v = pt.trackLen[app_.curTrack()];
     if (v) snprintf(o, n, "%u", v); else snprintf(o, n, "OFF");
   },
   [this](int d) {
     mt::Pattern& pt = app_.project().patterns[app_.editPattern()];
     uint8_t& v = pt.trackLen[app_.curTrack()];
     app_.pushUndo();  // whole-pattern snapshot (see App::pushUndo)
     engine::lockProject();
     v = static_cast<uint8_t>(clampi(v + d, 0, pt.length));
     engine::unlockProject();
     app_.markDirty();
   }},
```

**Step 4 — GRID boundary.** `drawOverview` row loop: `const uint8_t tl = pt.trackLen[tr]; const bool past = tl && step >= tl;` → text colour `kDim` when `past`; when `tl && step == tl` draw `s.drawFastHLine(x, y, kColW, kCursor)`. Same in `drawDetail` for the current track (full width).

**Step 5:** `pio run -e wt32` → compiles. `pio test -e native` → PASS.

---

## Part B — Live

### Task 6: Scenes model + `SCNS` chunk + BANK scene tiles

**Files:**
- Modify: `lib/core/src/model.h` (`scenes` — added in Task 3; `kSceneEmpty`), `lib/core/src/project_io.cpp`
- Modify: `src/ui/bank_screen.h/.cpp` (tiles under the chain list)
- Test: `test/test_project_io/test_main.cpp`

**Step 1: Test**

```cpp
void test_scns_round_trip_and_default() {
  a.reset();
  a.scenes[0] = 0x0005; a.scenes[7] = 0x8000;
  VecSink out;
  TEST_ASSERT_TRUE(saveProject(a, out));
  VecSource in(out.data);
  TEST_ASSERT_EQUAL(static_cast<int>(LoadErr::Ok), static_cast<int>(loadProject(in, b)));
  TEST_ASSERT_EQUAL_HEX16(0x0005, b.scenes[0]);
  TEST_ASSERT_EQUAL_HEX16(0x8000, b.scenes[7]);
  TEST_ASSERT_EQUAL_HEX16(kSceneEmpty, b.scenes[3]);
  std::vector<uint8_t> f = withoutChunks(out.data, {"SCNS"});
  TEST_ASSERT_EQUAL(static_cast<int>(LoadErr::Ok), static_cast<int>(loadBytes(f)));
  TEST_ASSERT_EQUAL_HEX16(kSceneEmpty, b.scenes[0]);
}
```

**Step 2:** FAIL. **Step 3:** `SCNS` = 16 bytes (8 × LE uint16), read: size must be 16 else `BadValue`; always written. Dispatch `"SCNS"`.

BANK: `kSceneY = y0 + kHeadH + kRows * kRowH` is past the list — reserve the last chain row: `kRows - 1` list rows, the freed 24-px strip holds 8 tiles of 56 px (`S1..S8`, filled background when stored, `kDim` outline when empty). Touch in `chainTouch`: tile hit → `Tap`: recall (`for t: tracks[t].mute = (m >> t) & 1` under lock, `markDirty`, toast `SCENE n`); `LongPress`: store (`scenes[i] = mask of tracks[t].mute`); Tap with Shift: `scenes[i] = kSceneEmpty`. Recall on an empty tile: nothing.

**Step 4:** suite PASS, `pio run -e wt32` compiles.

---

### Task 7: Fill — CND `FIL` / `NFL`, `setFill`, Shift + Play hold

**Files:**
- Modify: `lib/core/src/model.h` (`kCndFill`, `kCndNoFill`), `lib/core/src/fx_info.cpp` (`cndIndex`, `cndValue`, `kCndCount`, `fxFormat`), `lib/core/src/step_expand.h/.cpp` (`ExpandCtx::fill`, `cndPasses`)
- Modify: `lib/core/src/sequencer.h/.cpp` (`setFill`, `fill_`, ctx)
- Modify: `src/hw/input.h/.cpp` (`PlayRelease`), `src/engine/engine.h/.cpp` (`Cmd::Fill`, `Status::fill`), `src/ui/app.cpp` (`:72-90`, status bar)
- Test: `test/test_expand/test_main.cpp`, `test/test_fx_info/test_main.cpp`, `test/test_sequencer/test_main.cpp`

**Step 1: Tests**

```cpp
// test_expand
void test_cnd_fill_values() {
  Step s; s.note = 60; s.fx[0] = {Fx::CND, kCndFill};
  TrackCfg t; Rng rng(1); ExpandOut out;
  ExpandCtx on{125000, 5, 0, ScaleType::Chromatic, 24}; on.fill = true;
  ExpandCtx off = on; off.fill = false;
  TEST_ASSERT_TRUE(expandStep(s, t, on, rng, out));
  TEST_ASSERT_FALSE(expandStep(s, t, off, rng, out));
  s.fx[0].val = kCndNoFill;
  TEST_ASSERT_FALSE(expandStep(s, t, on, rng, out));
  TEST_ASSERT_TRUE(expandStep(s, t, off, rng, out));
}
// test_fx_info: the encoder order ends FST, 1:2 ... 8:8, FIL, NFL
void test_cnd_order_has_fill() {
  uint8_t v = 0x88;  // 8:8, the last A:B
  v = fxStep(Fx::CND, v, 1); TEST_ASSERT_EQUAL_HEX8(kCndFill, v);
  v = fxStep(Fx::CND, v, 1); TEST_ASSERT_EQUAL_HEX8(kCndNoFill, v);
  v = fxStep(Fx::CND, v, 1); TEST_ASSERT_EQUAL_HEX8(kCndNoFill, v);  // clamped
  char out[5];
  fxFormat(Fx::CND, kCndFill, out); TEST_ASSERT_EQUAL_STRING("FIL", out);
  fxFormat(Fx::CND, kCndNoFill, out); TEST_ASSERT_EQUAL_STRING("NFL", out);
}
// test_sequencer
void test_fill_gates_fil_steps() {
  p->patterns[0].length = 4;
  p->patterns[0].steps[0][0].note = 60;
  p->patterns[0].steps[0][0].fx[0] = {Fx::CND, kCndFill};
  seq->start(0, *sink);
  run(0, 510000);
  TEST_ASSERT_EQUAL(0, sink->times(0x90, 60).size());
  seq->setFill(true);
  run(510001, 1010000);
  TEST_ASSERT_EQUAL(1, sink->times(0x90, 60).size());
}
```

**Step 2:** FAIL. **Step 3:**

`model.h`: `constexpr uint8_t kCndFill = 0x01, kCndNoFill = 0x02;  // CND: low nibble < 2 is never an A:B value`.

`step_expand.cpp`:

```cpp
bool cndPasses(uint8_t v, uint32_t loop, bool fill) {
  if (v == 0) return loop == 0;  // FST
  if (v == kCndFill) return fill;
  if (v == kCndNoFill) return !fill;
  const uint32_t a = v >> 4, b = v & 15;
  if (b == 0) return true;
  return loop % b == a - 1;
}
```

`ExpandCtx`: `bool fill = false;`. `fx_info.cpp`: `kCndCount = 38`; `cndIndex`: `kCndFill → 36`, `kCndNoFill → 37`; `cndValue`: `36 → kCndFill`, `37 → kCndNoFill` (before the `0x88` fallback); `fxFormat`: `"FIL"` / `"NFL"`. Sequencer: `bool fill_ = false; void setFill(bool on) { fill_ = on; } bool fill() const`; both `ExpandCtx` constructions set `.fill = fill_` (make `ExpandCtx` construction a small helper `ctx(su)` to avoid the duplicate).

Input: `InputType::PlayRelease` emitted on the Play button's release (`input.cpp` already debounces Play for `PlayPress`; add the falling-edge event). Engine: `Cmd::Fill` (arg 1 / 0) → `seq->setFill(arg)`; `Status::fill`. `app.cpp` `PlayPress` with `shift_` while `status().playing`: `engine::post(Cmd::Fill, 1); fillDownMs_ = now;` and do **not** toggle; on `PlayRelease` with `fillDownMs_`: `post(Cmd::Fill, 0)`; if held `< hw::kLongPressMs` also `post(Cmd::TogglePlay)` (the old Shift + Play pause). Without Shift or when not playing, behaviour as today. Status bar: draw `FILL` in `kCursor` in place of the `L` counter while `status().fill`.

**Step 4:** suite PASS, `pio run -e wt32` compiles. Update `docs/manual.html` CND table (FIL / NFL) and the Shift + Play row.

---

### Task 8: `TrackRelease` events

**Files:**
- Modify: `src/hw/input.h` (`InputType::TrackRelease`), `src/hw/trackio.cpp` (`:35-60`, the debounce loop), `src/ui/app.cpp` (`:94`, dispatch)

**Step 1:** In `trackio.cpp`, where the debounced `state` changes and `TrackPress` events are queued for bits going 0→1, also queue `{InputType::TrackRelease, n, shift}` for bits going 1→0. `app.cpp` `onInput`: `case InputType::TrackRelease: if (!menu_.isOpen()) trackRelease(ev.delta); return;` with `App::trackRelease(int n)` forwarding to `grid_.trackRelease(n)` on the GRID tab (used by Task 11; empty until then).

**Step 2:** `pio run -e wt32` compiles.

---

### Task 9: `phase256` + `recordStepFor`

**Files:**
- Create: `lib/core/src/record.h`
- Modify: `lib/core/src/sequencer.h/.cpp` (`phase256`), `src/engine/engine.h/.cpp` (`Status::phase`)
- Test: `test/test_record/test_main.cpp` (new), `test/test_sequencer/test_main.cpp`

**Step 1: Tests**

```cpp
// test_record
void test_record_step_rounds_to_nearest() {
  TEST_ASSERT_EQUAL(3, recordStepFor(3, 0, 16));
  TEST_ASSERT_EQUAL(3, recordStepFor(3, 127, 16));
  TEST_ASSERT_EQUAL(4, recordStepFor(3, 128, 16));
  TEST_ASSERT_EQUAL(0, recordStepFor(15, 200, 16));  // wraps
}
// test_sequencer
void test_phase256_within_step() {
  p->patterns[0].length = 4;
  seq->start(0, *sink);
  run(0, 1000);
  TEST_ASSERT_EQUAL(0, seq->phase256(0));
  TEST_ASSERT_EQUAL(128, seq->phase256(62500));  // half a 16th at 120 BPM
}
```

**Step 2:** FAIL. **Step 3:** `record.h`:

```cpp
#pragma once
#include <stdint.h>
namespace mt {
// Step a live-recorded note lands on: the heard step, or the next one past the half (phase 0..255).
inline int recordStepFor(int pos, uint8_t phase, int len) {
  if (len <= 0) return 0;
  return phase < 128 ? pos % len : (pos + 1) % len;
}
}  // namespace mt
```

Sequencer: `uint8_t phase256(uint64_t now) const` — `heardStepT_` (time of the heard step start, set in `dispatch` where `heardPos_` is updated) and `stepUs()`: `now <= heardStepT_ ? 0 : min(255, (now - heardStepT_) * 256 / stepUs())`. Engine `publish()` fills `st.phase = seq->phase256(nowUs())`.

**Step 4:** PASS, compiles.

---

### Task 10: GRID `Rec` mode

**Files:**
- Modify: `src/ui/grid_screen.h/.cpp` (`MenuId::kRec`, `rec_`, `trackKey`, title, menu)

**Step 1:** `rec_` flag, menu item `Rec: ON/OFF` (`kRec`), toggling it clears `perf_` (Task 11) and `edit_`. Title: when `rec_` draw `REC` in red (`kRecColor` = `0xF800` in `theme.h` if absent) before the track name.

`trackKey(n, shift)`:

```cpp
  if (rec_ && app_.status().playing && !edit_) {
    const engine::Status& st = app_.status();
    if (st.pattern != app_.editPattern()) return true;  // recording into the heard pattern only
    const int step = mt::recordStepFor(st.pos, st.phase, len());
    if (st.loop != recLoop_) { app_.pushUndo(); recLoop_ = st.loop; }  // one snapshot per pass
    mt::Step s = pat().steps[track()][step];
    if (shift) s.note = mt::kNoteEmpty;
    else s.note = degreeNote(n);  // factor the note computation out of enterDegree (button -> note)
    engine::lockProject();
    pat().steps[track()][step] = s;
    engine::unlockProject();
    app_.markDirty();
    return true;
  }
```

`degreeNote(n)` = the existing scale-degree + octave logic of `enterDegree` without the write / cursor move (`enterDegree` calls it). `recLoop_` is `uint32_t`, reset to `UINT32_MAX` when Rec turns on.

**Step 2:** `pio run -e wt32` compiles; `pio test -e native` PASS (no core change).

---

### Task 11: Punch-in `Perf` fx

**Files:**
- Modify: `lib/core/src/model.h` (`PerfFx`), `lib/core/src/sequencer.h/.cpp` (`perf_[kTracks]`, `perfOn/Off`, `adjustStep`, mute)
- Modify: `src/engine/engine.h/.cpp` (`Cmd::PerfOn` arg = track | fx << 8, `Cmd::PerfOff`)
- Modify: `src/ui/grid_screen.h/.cpp` (`perf_`, menu `Perf: ON/OFF`, `trackKey` / `trackRelease`, title `PERF`)
- Test: `test/test_sequencer/test_main.cpp`

**Step 1: Tests**

```cpp
void test_perf_rat2_doubles_and_release_restores() {
  p->patterns[0].length = 4;
  p->patterns[0].steps[0][0].note = 60;
  seq->start(0, *sink);
  seq->perfOn(0, PerfFx::Rat2);
  run(0, 510000);
  TEST_ASSERT_EQUAL(2, sink->times(0x90, 60).size());
  seq->perfOff(0);
  run(510001, 1010000);
  TEST_ASSERT_EQUAL(3, sink->times(0x90, 60).size());
}

void test_perf_mute_silences_track() {
  p->patterns[0].length = 4;
  p->patterns[0].steps[0][0].note = 60;
  seq->perfOn(0, PerfFx::Mute);
  seq->start(0, *sink);
  run(0, 510000);
  TEST_ASSERT_EQUAL(0, sink->times(0x90, 60).size());
}

void test_perf_synth_fx_skipped_on_midi_track() {
  p->patterns[0].length = 4;
  p->patterns[0].steps[0][0].note = 60;
  seq->perfOn(0, PerfFx::FltLow);
  seq->start(0, *sink);
  run(0, 10000);
  TEST_ASSERT_EQUAL(1, sink->times(0x90, 60).size());
  TEST_ASSERT_EQUAL(0, sink->synKind(0xF5).size());  // no synth fx on a MIDI track
}
```

**Step 2:** FAIL. **Step 3:**

`model.h`: `enum class PerfFx : uint8_t { None, Rat2, Rat4, FltLow, FltHigh, DlyMax, DecShort, Fade, Mute, Count };`.

`sequencer.h`: `PerfFx perf_[kTracks] = {}; void perfOn(int track, PerfFx fx); void perfOff(int track); static FxSlot perfSlot(PerfFx fx);`.

`sequencer.cpp`:

```cpp
FxSlot Sequencer::perfSlot(PerfFx fx) {
  switch (fx) {
    case PerfFx::Rat2: return {Fx::RAT, 2};
    case PerfFx::Rat4: return {Fx::RAT, 4};
    case PerfFx::FltLow: return {Fx::FLT, 30};
    case PerfFx::FltHigh: return {Fx::FLT, 120};
    case PerfFx::DlyMax: return {Fx::DLY, 127};
    case PerfFx::DecShort: return {Fx::DCY, 20};
    case PerfFx::Fade: return {Fx::VSL, static_cast<uint8_t>(-16)};
    default: return {Fx::None, 0};
  }
}

void Sequencer::perfOn(int track, PerfFx fx) {
  if (track < 0 || track >= kTracks) return;
  perf_[track] = fx;
}
void Sequencer::perfOff(int track) {
  if (track >= 0 && track < kTracks) perf_[track] = PerfFx::None;
}
```

`adjustStep` (after the transpose):

```cpp
  const FxSlot pf = perfSlot(perf_[track]);
  if (pf.cmd != Fx::None && !(fxSynthOnly(pf.cmd) && !internal(track))) {
    int slot = kFxSlots - 1;
    for (int k = 0; k < kFxSlots; ++k)
      if (s.fx[k].cmd == Fx::None || s.fx[k].cmd == pf.cmd) { slot = k; break; }
    s.fx[slot] = pf;
  }
```

Mute: in `scheduleStep` / `skipStep`, the track is skipped when `perf_[tr] == PerfFx::Mute` (treat like `!trackAudible`); on the first muted step `pushOff(tr, t)` (track a `perfMuted_` bit to call it once). `perfOff` of Mute: nothing to do, the next step plays. `stop()` clears `perf_`.

Engine: `Cmd::PerfOn` → `seq->perfOn(arg & 0xFF, static_cast<PerfFx>(arg >> 8))`, `Cmd::PerfOff` → `seq->perfOff(arg)`.

GRID: `perf_` flag, menu `Perf: ON/OFF` (turning on clears `rec_` and `edit_`), title `PERF` in `kCursor`. `trackKey(n, shift)`: `if (perf_ && !shift && app_.status().playing) { engine::post(Cmd::PerfOn, track() | ((n + 1) << 8)); return true; }`. New `void trackRelease(int n)`: `if (perf_) engine::post(Cmd::PerfOff, track());`. `App::trackRelease` (Task 8) calls it on the GRID tab.

**Step 4:** `pio test -e native` → PASS; `pio run -e wt32` → compiles.

---

### Task 12: Docs

- `README.md`: song mode items (transpose, repeat, scene), per-track length, fill (hold Shift + Play), scenes, REC, PERF with the button table.
- `docs/manual.html`: BANK chain fields and scene tiles; TRACK `Pat len`; GRID `Rec` / `Perf` menu items and title badges; CND `FIL` / `NFL`; status bar `FILL`; the Shift + Play change (short = pause, held = fill).
- Final: `pio test -e native` → all PASS; `pio run -e wt32` → compiles. Summarize what was built and anything left unverified on hardware (button release timing, LED refresh).
