deemonoise/D-TRK/docs/plans/2026-10-06-sound-fx.md

# Sound Fx Implementation Plan (drive, reverb, compressor, ARP modes, velocity)

> **For Claude:** REQUIRED SUB-SKILL: Use superpowers:executing-plans to implement this plan task-by-task.

**Goal:** Per-instrument drive and reverb send, a master compressor with a sidechain track, an arpeggiator with modes / rate / chord cycling, velocity → cutoff / DECAY. Old projects and presets sound unchanged.

**Architecture:** Three hardware-free DSP units in `lib/core` (`synth_drive.h`, `synth_reverb.*`, `synth_comp.*`) hooked into `Synth::render`: drive per voice before the filter; reverb from an `rsend_` bus like the delay; the compressor on the mix after the returns, keyed by the mix plus an `sc_` bus of the sidechain track's voices. New lock bits (`uint16_t lockMask`) and fx `DRV`, `RVB`, `ARM`; ARP state in `TrackRt` grows a mode / rate and a chord note list. New bytes go into reserved slots of the `FMIN` record and appended `AUDI` bytes.

**Tech Stack:** C++17, PlatformIO native tests (Unity, `pio test -e native -f <suite>`), ESP32-S3 Arduino (`pio run -e wt32`). Design: `docs/plans/2026-10-06-sound-fx-design.md`.

**Rules:** no commits (the user commits). Run **after** the SYNTH / wavetable work is merged (it edits `synth.cpp`, `synth_voice.h`, `model.h`, `inst_screen.cpp`); if a merge conflict appears in those files keep both sides. Assumes blocks 1–3 (16 tracks, KIT, song + live) are in. Do not stop for hardware checks; finish, then summarize.

---

### Task 1: Model, lock bits, fx names

**Files:**
- Modify: `lib/core/src/model.h` (LockBit, Fx, LfoDest, Instrument, Project), `lib/core/src/model.cpp` (`Project::reset`, `lfoDestStep` bounds), `lib/core/src/fx_info.cpp`
- Modify: `lib/core/src/synth_voice.h:58-59`, `lib/core/src/synth.h` (`TrackRt::lockMask`, `lock[]`)
- Test: `test/test_fx_info/test_main.cpp`, `test/test_model/test_main.cpp`

**Step 1: Failing tests**

`test_fx_info`:
```cpp
void test_new_fx_names_and_order() {
  TEST_ASSERT_EQUAL_STRING("DRV", fxName(Fx::DRV));
  TEST_ASSERT_EQUAL_STRING("RVB", fxName(Fx::RVB));
  TEST_ASSERT_EQUAL_STRING("ARM", fxName(Fx::ARM));
  TEST_ASSERT_EQUAL(static_cast<int>(Fx::ARM), static_cast<int>(fxNextCmd(Fx::RVB, 1)));
  TEST_ASSERT_EQUAL(static_cast<int>(Fx::None), static_cast<int>(fxNextCmd(Fx::ARM, 1)));
  TEST_ASSERT_TRUE(fxSynthOnly(Fx::DRV) && fxSynthOnly(Fx::RVB) && fxSynthOnly(Fx::ARM));
  TEST_ASSERT_EQUAL(0x03, fxDefault(Fx::ARM));
}
void test_arm_format_and_step() {
  char o[5];
  fxFormat(Fx::ARM, 0x03, o); TEST_ASSERT_EQUAL_STRING(" U3", o);
  fxFormat(Fx::ARM, 0x14, o); TEST_ASSERT_EQUAL_STRING(" D4", o);
  fxFormat(Fx::ARM, 0x22, o); TEST_ASSERT_EQUAL_STRING(" B2", o);
  fxFormat(Fx::ARM, 0x38, o); TEST_ASSERT_EQUAL_STRING(" R8", o);
  TEST_ASSERT_EQUAL_HEX8(0x04, fxStep(Fx::ARM, 0x03, 1));   // rate first
  TEST_ASSERT_EQUAL_HEX8(0x11, fxStep(Fx::ARM, 0x08, 1));   // rate 8 -> next mode, rate 1
  TEST_ASSERT_EQUAL_HEX8(0x38, fxStep(Fx::ARM, 0x38, 1));   // clamps at R8
  TEST_ASSERT_EQUAL_HEX8(0x01, fxStep(Fx::ARM, 0x01, -1));  // clamps at U1
}
```
`test_model`: defaults `drive == 0, rsend == 0, velCut == 0, velMac == 0`; `rvbSize 60, rvbDamp 70, rvbLevel 80, compAmt 0, compRel 50, scTrack 0, scDepth 64`; `kLocks == 10`; `lfoDestStep(Cutoff, 1, false) == Drive`, `lfoDestStep(Drive, 1, true) == Drive`.

**Step 2:** `pio test -e native -f test_fx_info` → FAIL (`DRV` undeclared).

**Step 3: Implement**

`model.h`:
```cpp
enum LockBit : uint8_t { kLockFlt = kFmMacros, kLockRes, kLockDly, kLockDrv, kLockRvb, kLocks };
static_assert(kLocks <= 16, "lockMask is a uint16_t");
enum class LfoDest : uint8_t { Pitch, Dec, Col, Shp, Swp, Con, Vol, Cutoff, Drive, Count };
// Fx: ... SLC, OFF, DLY, DRV, RVB, ARM, Count
// ARM: mode << 4 | rate (1..8); modes UP, DOWN, UPDOWN, RANDOM. kArmDefault = UP x3 (today's ARP).
constexpr uint8_t kArmModes = 4, kArmRateMax = 8, kArmDefault = 0x03;
// Synth message 0xF5 kSynthArpChord chord: the next ARP of the track cycles this chord (CHD value).
constexpr uint8_t kSynthArpChord = 0xF1;
```
`Instrument`: `uint8_t drive = 0; uint8_t rsend = 0; int8_t velCut = 0; int8_t velMac = 0;` after `send`.
`Project`: `uint8_t rvbSize = 60, rvbDamp = 70, rvbLevel = 80; uint8_t compAmt = 0, compRel = 50, scTrack = 0, scDepth = 64;` after `dlyLevel`; `reset()` sets them.
`synth_voice.h:58` and `synth.h` TrackRt: `uint16_t lockMask = 0; uint8_t lock[kLocks]`. Every `1 << k` on a lockMask: `1u << k` (fits uint16).

`fx_info.cpp` `kInfo` append:
```cpp
    {"DRV", "DRIVE", 0, 127, 64, false},
    {"RVB", "REVERB SEND", 0, 127, 64, false},
    {"ARM", "ARP MODE", 0, 0, kArmDefault, false},  // own ordering: rate 1..8 then mode
```
`fxFormat`: `case Fx::ARM: snprintf(out, 5, " %c%u", "UDBR"[(v >> 4) & 3], (v & 15) < 1 ? 1 : ((v & 15) > 8 ? 8 : v & 15)); return;`
`fxStep` for ARM: index `i = mode * 8 + (rate - 1)`, `i += delta`, clamp 0..31, back to `((i / 8) << 4) | (i % 8 + 1)`.
`fxSynthOnly`: `(f >= Fx::SLD && f <= Fx::SLC) || f == Fx::DLY || f >= Fx::DRV`.
`lfoDestStep`: `kLast = Count - 1` already follows the enum; macros = false must skip Dec..Con but reach Drive — check the function body, adjust the skip range only.

**Step 4:** `pio test -e native -f test_fx_info`, `-f test_model` → PASS. Then `pio test -e native` → every other suite still passes (lockMask width is internal).

---

### Task 2: Drive DSP

**Files:** Create `lib/core/src/synth_drive.h`, `test/test_synth_drive/test_main.cpp`.

**Step 1: Failing test**
```cpp
#include <unity.h>
#include <math.h>
#include "synth_drive.h"
using namespace mt;
void setUp() {} void tearDown() {}
void test_drive_zero_is_identity() {
  Drive d; d.set(0);
  for (float x : {-1.5f, -0.3f, 0.f, 0.25f, 1.f}) TEST_ASSERT_EQUAL_FLOAT(x, d.process(x));
  TEST_ASSERT_FALSE(d.on());
}
void test_drive_saturates_and_is_monotonic() {
  Drive d; d.set(127);
  TEST_ASSERT_TRUE(d.on());
  float prev = -2;
  for (int i = -40; i <= 40; ++i) {
    const float y = d.process(i * 0.1f);
    TEST_ASSERT_TRUE(y >= prev - 1e-6f); prev = y;
    TEST_ASSERT_TRUE(fabsf(y) <= 1.0001f);
  }
  TEST_ASSERT_FLOAT_WITHIN(0.01f, 1.f, d.process(1.f));          // normalized: tanh(g)/tanh(g)
  TEST_ASSERT_FLOAT_WITHIN(0.02f, tanhf(0.8f) / tanhf(8.f), d.process(0.1f));
}
int main() { UNITY_BEGIN(); RUN_TEST(test_drive_zero_is_identity); RUN_TEST(test_drive_saturates_and_is_monotonic); return UNITY_END(); }
```

**Step 2:** `pio test -e native -f test_synth_drive` → FAIL (no header).

**Step 3: Implement** `synth_drive.h`:
```cpp
#pragma once
#include <math.h>
#include <stdint.h>
namespace mt {
// tanh waveshaper: y = tanh(g x) / tanh(g), g = 1..8 from drive 0..127; drive 0 = bypass (bit-exact).
// 257-point table over [-8, 8], linear interpolation; no transcendental per sample.
class Drive {
 public:
  static constexpr int kTab = 257;
  void set(uint8_t drive) {  // per control update
    g_ = drive ? 1.f + (drive > 127 ? 127 : drive) * (7.f / 127.f) : 0.f;
    norm_ = drive ? 1.f / tanhf(g_) : 1.f;
  }
  bool on() const { return g_ != 0.f; }
  float process(float x) const {
    if (!on()) return x;
    float u = x * g_;
    u = u < -8.f ? -8.f : (u > 8.f ? 8.f : u);
    const float p = (u + 8.f) * 16.f;         // table position 0..256
    const int i = static_cast<int>(p);
    const float f = p - i;
    const float* t = table();
    const float a = t[i], b = t[i + 1 < kTab ? i + 1 : kTab - 1];
    return (a + (b - a) * f) * norm_;
  }
 private:
  static const float* table() {
    static float t[kTab];
    static bool init = false;
    if (!init) { for (int i = 0; i < kTab; ++i) t[i] = tanhf(-8.f + i * (1.f / 16.f)); init = true; }
    return t;
  }
  float g_ = 0, norm_ = 1;
};
}  // namespace mt
```
(The table is built on first use from the audio task — 257 `tanhf` once, ~50 µs; acceptable. If the first block must be clean, call `Drive().set(1)` in `Synth`'s constructor.)

**Step 4:** `pio test -e native -f test_synth_drive` → PASS.

---

### Task 3: Drive in the voice (lock, LFO, render)

**Files:** `lib/core/src/synth_voice.h` (add `Drive drive; uint8_t vel = 0;`), `lib/core/src/synth.cpp` (`fx()` lock case, `control()`, `lfo()` dest, `renderVoice`), `test/test_synth/test_main.cpp`.

**Step 1: Failing tests** (use the file's helpers that render a note and inspect the output):
- `test_drive_zero_bit_exact`: render a CHIP saw note with `drive = 0`, compare the buffer to a render on a copy where the instrument is identical — identical by construction; more useful: render with `drive = 0` before and after this task (keep a golden: sum of |samples| of the existing `test_chip_*` output must not change — reuse an existing test's expected values).
- `test_drive_changes_waveform`: same note with `drive = 127`: peak ≤ amp, RMS higher than with drive 0 (the saw squares up).
- `test_drv_lock_on_note_step`: `0xF5 kSynthStep`, `0xF5 DRV 127`, note-on → `voice(v).drive.on()`; a second track's voice unaffected.
- `test_lfo_drive_dest`: `lfoDest = Drive`, depth 63, drive 64: `drive.on()` flips on/off over a cycle at rate where the LFO swings below 0 — assert `on()` differs between two control points.

**Step 2:** `pio test -e native -f test_synth` → FAIL.

**Step 3: Implement**
- `noteOn` (`synth.cpp:345`): `v.vel = vel;` next to `v.gain = …`.
- `fx()` lock case: add `case Fx::DRV: case Fx::RVB:` and
  ```cpp
  const int k = cmd == static_cast<uint8_t>(Fx::DLY) ? kLockDly
              : cmd == static_cast<uint8_t>(Fx::DRV) ? kLockDrv
              : cmd == static_cast<uint8_t>(Fx::RVB) ? kLockRvb : cmd - static_cast<uint8_t>(Fx::DCY);
  ```
- `lfo()` returns the LFO value; `control()` routes it by dest: where `lfoCut` is derived add `float lfoDrv = dest == Drive ? l * 64 : 0` (±64 drive units at full depth, like cutoff).
- `control()` after the send line (`:494`):
  ```cpp
  const uint8_t drv = (v.lockMask & (1u << kLockDrv)) ? v.lock[kLockDrv] : m.drive;
  v.drive.set(static_cast<uint8_t>(clampf(drv + lfoDrv, 0.f, 127.f)));
  const uint8_t rs = (v.lockMask & (1u << kLockRvb)) ? v.lock[kLockRvb] : m.rsend;
  v.rsend = (rs > 127 ? 127 : rs) * (1.f / 127.f);
  ```
  (`Voice::rsend` float is added in Task 5; add the field now, use in Task 5.)
- `renderVoice`: when `v.drive.on()`, render the engine into `flt[]` even without the filter, then
  ```cpp
  if (v.drive.on()) for (int i = 0; i < n; ++i) flt[i] = v.drive.process(flt[i]);
  if (v.fltOn) for (...) out[i] += v.flt.process(flt[i]);
  else if (v.drive.on()) for (...) out[i] += flt[i];
  ```
  i.e. `dst = flt` when `v.fltOn || v.drive.on()`. Drive off and filter off: the old direct path, bit-exact.

**Step 4:** `pio test -e native -f test_synth` → PASS (all, including old ARP / filter tests).

---

### Task 4: Reverb DSP

**Files:** Create `lib/core/src/synth_reverb.h`, `lib/core/src/synth_reverb.cpp`, `test/test_synth_reverb/test_main.cpp`.

**Step 1: Failing tests**
```cpp
static float buf[Reverb::kBufLen];
void test_silent_without_buffer() { Reverb r; float in[128] = {1}, mix[128] = {0}; r.process(in, mix, 128, 60, 70, 127); for (float x : mix) TEST_ASSERT_EQUAL_FLOAT(0.f, x); }
void test_level_zero_bit_exact() { Reverb r; r.setBuffer(buf, Reverb::kBufLen); float in[128] = {1}, mix[128]; for (int i = 0; i < 128; ++i) mix[i] = i * 0.001f; float ref[128]; memcpy(ref, mix, sizeof ref); r.process(in, mix, 128, 60, 70, 0); TEST_ASSERT_EQUAL_FLOAT_ARRAY(ref, mix, 128); }
// Impulse: tail present after 50 ms, below -60 dB (1e-3 of the peak) within 3 s at size 60.
void test_impulse_tail_decays() { ... feed 1 at sample 0 then zeros in 128-blocks for 3 s; track peak per 100 ms; assert peak(50..150 ms) > 0.01, peak(2.9..3.0 s) < 1e-3 * overall peak ... }
void test_size_lengthens_tail() { ... time when the 100 ms peak first drops below 1e-3 at size 0 < at size 127 ... }
```

**Step 2:** `pio test -e native -f test_synth_reverb` → FAIL.

**Step 3: Implement**

`synth_reverb.h`:
```cpp
#pragma once
#include <stdint.h>
namespace mt {
// Freeverb-lite mono reverb: 4 parallel damped feedback combs, 2 series allpasses. Float buffer
// (kBufLen floats) handed in by the caller (PSRAM on the device); no buffer = silent.
class Reverb {
 public:
  static constexpr int kCombs = 4, kAllpasses = 2;
  static constexpr int kCombLen[kCombs] = {1116, 1188, 1277, 1356};
  static constexpr int kApLen[kAllpasses] = {556, 441};
  static constexpr int kBufLen = 1116 + 1188 + 1277 + 1356 + 556 + 441;  // 5934
  void setBuffer(float* buf, int len);  // len must be >= kBufLen, else off
  void clear();
  // mix[i] += wet * level / 127 * 0.5. size / damp / level 0..127.
  void process(const float* in, float* mix, int n, uint8_t size, uint8_t damp, uint8_t level);
 private:
  float* buf_ = nullptr;
  float* comb_[kCombs] = {};
  float* ap_[kAllpasses] = {};
  int combIdx_[kCombs] = {}, apIdx_[kAllpasses] = {};
  float store_[kCombs] = {};
  int combLen_[kCombs] = {};  // current (size-scaled) lengths
};
}
```
`synth_reverb.cpp`:
```cpp
void Reverb::setBuffer(float* buf, int len) {
  buf_ = len >= kBufLen ? buf : nullptr;
  if (!buf_) return;
  float* p = buf_;
  for (int c = 0; c < kCombs; ++c) { comb_[c] = p; p += kCombLen[c]; }
  for (int a = 0; a < kAllpasses; ++a) { ap_[a] = p; p += kApLen[a]; }
  clear();
}
void Reverb::clear() {
  if (!buf_) return;
  for (int i = 0; i < kBufLen; ++i) buf_[i] = 0;
  for (int c = 0; c < kCombs; ++c) { combIdx_[c] = 0; store_[c] = 0; combLen_[c] = kCombLen[c]; }
  for (int a = 0; a < kAllpasses; ++a) apIdx_[a] = 0;
}
void Reverb::process(const float* in, float* mix, int n, uint8_t size, uint8_t damp, uint8_t level) {
  if (!buf_ || level == 0) return;
  const float sz = (size > 127 ? 127 : size) * (1.f / 127.f);
  const float fb = 0.70f + 0.28f * sz;
  const float d = (damp > 127 ? 127 : damp) * (0.4f / 127.f);
  const float wet = (level > 127 ? 127 : level) * (0.5f / 127.f);
  for (int c = 0; c < kCombs; ++c) {
    const int len = static_cast<int>(kCombLen[c] * (0.5f + 0.5f * sz));
    combLen_[c] = len < 1 ? 1 : len;
    if (combIdx_[c] >= combLen_[c]) combIdx_[c] = 0;
  }
  for (int i = 0; i < n; ++i) {
    const float x = in[i] * 0.25f;  // comb input gain (4 combs sum)
    float acc = 0;
    for (int c = 0; c < kCombs; ++c) {
      float* line = comb_[c];
      const float out = line[combIdx_[c]];
      store_[c] = out * (1.f - d) + store_[c] * d;
      line[combIdx_[c]] = x + store_[c] * fb;
      if (++combIdx_[c] >= combLen_[c]) combIdx_[c] = 0;
      acc += out;
    }
    for (int a = 0; a < kAllpasses; ++a) {
      float* line = ap_[a];
      const float b = line[apIdx_[a]];
      line[apIdx_[a]] = acc + b * 0.5f;
      acc = b - acc * 0.5f;  // allpass, g = 0.5 (Freeverb form)
      if (++apIdx_[a] >= kApLen[a]) apIdx_[a] = 0;
    }
    mix[i] += acc * wet;
  }
}
```
(`static constexpr int` arrays need an out-of-line definition in the .cpp for C++17 odr-use: `constexpr int Reverb::kCombLen[Reverb::kCombs];` — or make them `inline constexpr` at namespace scope.)

**Step 4:** `pio test -e native -f test_synth_reverb` → PASS. Tune `fb` / `d` only if the decay test fails (keep -60 dB < 3 s at size 60).

---

### Task 5: Reverb bus in the synth

**Files:** `lib/core/src/synth.h` (`float rsend_[kBlock]; Reverb reverb_; setReverbBuffer`), `lib/core/src/synth.cpp` (`render`, `reset`), `lib/core/src/synth_voice.h` (`float rsend = 0;`), `src/audio/audio.cpp:533` (allocate `Reverb::kBufLen` floats in PSRAM next to the delay line), `test/test_synth/test_main.cpp`.

**Step 1: Failing tests** `test_rsend_zero_same_with_and_without_buffer` (bit-exact), `test_rsend_makes_tail` (note ends, output non-zero 300 ms later with `rsend 127` and a buffer; zero without), `test_rvb_lock_on_note_step` (like the DLY lock test).

**Step 2:** `pio test -e native -f test_synth` → FAIL.

**Step 3: Implement** `render()`:
```cpp
  for (auto& x : rsend_) x = 0;
  for (auto& x : sc_) x = 0;
  const int scTrack = p_.scTrack >= 1 && p_.scTrack <= kTracks ? p_.scTrack - 1 : -1;
  ...
    for (auto& v : voices_) {
      if (!v.on) continue;
      const bool bus = v.send > 0 || v.rsend > 0 || v.track == scTrack;
      if (bus) {
        float tmp[kControl] = {0};
        renderVoice(v, tmp, end - pos);
        for (int i = 0; i < end - pos; ++i) {
          mix_[pos + i] += tmp[i];
          send_[pos + i] += tmp[i] * v.send;
          rsend_[pos + i] += tmp[i] * v.rsend;
          if (v.track == scTrack) sc_[pos + i] += tmp[i];
        }
      } else renderVoice(v, mix_ + pos, end - pos);
  ...
  delay_.process(...);
  reverb_.process(rsend_, mix_, kBlock, p_.rvbSize, p_.rvbDamp, p_.rvbLevel);
```
(`sc_` is used in Task 6; declare it now.) `reset()`: `reverb_.clear()`. `audio.cpp`: `heap_caps_malloc(Reverb::kBufLen * sizeof(float), MALLOC_CAP_SPIRAM)` → `synth->setReverbBuffer`.

**Step 4:** `pio test -e native -f test_synth` → PASS; `pio run -e wt32` compiles.

---

### Task 6: Compressor DSP and master insert

**Files:** Create `lib/core/src/synth_comp.h`, `test/test_synth_comp/test_main.cpp`; modify `lib/core/src/synth.h/.cpp` (`Compressor comp_; float sc_[kBlock];`, `render()` before masterVol), `test/test_synth/test_main.cpp`.

**Step 1: Failing tests** (`test_synth_comp`):
- `test_bypass_bit_exact`: `amt 0` leaves a buffer untouched.
- `test_below_threshold_unity`: -20 dB (0.1 peak) sine, `amt 64` (T ≈ -18 dB): after 100 ms output peak == input peak × makeup within 1 %.
- `test_above_threshold_reduces`: 0 dB sine at `amt 64`: expected gain = -(0 - (-18)) × 0.75 = -13.5 dB + makeup 4.5 dB = -9 dB ± 1 dB after 100 ms.
- `test_sidechain_ducks`: quiet 0.1 sine in `mix`, loud 1.0 pulse in `sc`, `scDepth 127`: output drops by > 6 dB during the pulse vs before it.
`test_synth`: `test_comp_sidechain_track`: two tracks, `scTrack = 2`, a loud DRUM on track 2 ducks a sustained CHIP on track 1 (RMS of a window during the hit < 0.5 × RMS before, with `compAmt 100`).

**Step 2:** `pio test -e native -f test_synth_comp` → FAIL.

**Step 3: Implement** `synth_comp.h`:
```cpp
#pragma once
#include <math.h>
#include <stdint.h>
namespace mt {
// Master compressor: peak detector (1 ms attack, 20..1000 ms release), 4:1 above a threshold set by
// amt (-6 .. -30 dB), makeup = half the threshold drop. Gain computed every kHold samples, applied per
// sample. Key = mix, plus the sidechain bus weighted by scDepth. amt 0 = bypass (bit-exact).
class Compressor {
 public:
  static constexpr int kHold = 8;
  static constexpr float kRate = 32000.f;
  void reset() { env_ = 0; gain_ = 1; }
  void process(float* mix, const float* sc, int n, uint8_t amt, uint8_t rel, uint8_t scDepth) {
    if (amt == 0) return;
    const float a = amt > 127 ? 127 : amt;
    const float thrDb = -6.f - 24.f * a / 127.f;
    const float makeup = exp2f((-thrDb) * 0.5f / 6.02f);
    const float relMs = 20.f * powf(50.f, (rel > 127 ? 127 : rel) / 127.f);
    const float ca = 1.f - expf(-1.f / (0.001f * kRate));
    const float cr = 1.f - expf(-1.f / (relMs * 0.001f * kRate));
    const float scW = (scDepth > 127 ? 127 : scDepth) * (4.f / 127.f);
    for (int i = 0; i < n; ++i) {
      float key = fabsf(mix[i]);
      if (sc) key += fabsf(sc[i]) * scW;
      env_ += (key > env_ ? ca : cr) * (key - env_);
      if (i % kHold == 0) {
        const float envDb = env_ > 1e-6f ? 6.02f * log2f(env_) : -120.f;
        const float over = envDb - thrDb;
        gain_ = (over > 0 ? exp2f(-over * 0.75f / 6.02f) : 1.f) * makeup;
      }
      mix[i] *= gain_;
    }
  }
 private:
  float env_ = 0, gain_ = 1;
};
}
```
`render()`: after `reverb_.process(...)`: `comp_.process(mix_, scTrack >= 0 ? sc_ : nullptr, kBlock, p_.compAmt, p_.compRel, p_.scDepth);` then masterVol / soft clip as now. `reset()`: `comp_.reset()`.

**Step 4:** `pio test -e native -f test_synth_comp`, `-f test_synth` → PASS. Adjust the test tolerance, not the maths, if the attack/release constants land within 1.5 dB.

---

### Task 7: ARP modes and ARP + CHD

**Files:** `lib/core/src/synth.h` (`TrackRt`: `uint8_t arm = kArmDefault; uint8_t arpNotes[4]; uint8_t arpN = 0;`), `lib/core/src/synth.cpp` (`fx()`: `ARM`, `kSynthArpChord`; `control()` ARP block; reset on a new note step), `lib/core/src/step_expand.cpp:84-92` (ARP + CHD on INT), `lib/core/src/sequencer.cpp` (passes `kSynthArpChord` like other SynthFx — check `pushControls`: SynthFx events already go through as `0xF5 cmd val`; `cmd = kSynthArpChord` needs no change if the whole byte is forwarded), `test/test_synth/test_main.cpp`, `test/test_expand/test_main.cpp`.

**Step 1: Failing tests**
- `test_expand`: `test_arp_chd_int_emits_root_and_arpchord`: INT track, step with `CHD` (major) and `ARP 0x37`: events = SynthFx `kSynthArpChord` with the CHD value, then exactly one NoteOn (the root); `test_arp_chd_midi_full_chord`: MIDI track, same step: 3 NoteOns, no SynthFx; `test_arp_00_chd_normal`: INT, `ARP 00` + CHD: 3 NoteOns.
- `test_synth`: helper that samples `v.pitch`-derived output pitch is heavy; instead expose the ARP slot offset: add `int arpOffset(int v) const` (test hook, returns the current semitone offset of voice v's ARP) and assert over one step of 4 control points at rate 4: UP `0, x, y, 0`; DOWN `0, y, x, 0`; UPDOWN (`B`) with 3 notes `0, x, y, x`; RANDOM within `{0, x, y}`; chord mode with `kSynthArpChord` major (`0, 4, 7`): UP `0, 4, 7, 0`; existing ARP test unchanged (default `U3` = thirds of a step with `0, x, y`).

**Step 2:** `pio test -e native -f test_expand`, `-f test_synth` → FAIL.

**Step 3: Implement**

`step_expand.cpp` after `chordNotes(...)`:
```cpp
  // INT + ARP + CHD: the synth arpeggiates the chord from the root alone (kSynthArpChord sent above
  // with the fx; MIDI tracks have no ARP and keep the whole chord).
  if (t.out == TrackOut::Int) {
    const FxSlot* arp = s.find(Fx::ARP);
    if (arp && arp->val != 0 && nNotes > 1) {
      out.ev[out.count++] = {nudge0, EvKind::SynthFx, ch, kSynthArpChord, f->val};
      nNotes = 1;
    }
  }
```
(`nudge0` = the offset the other fx use; place the event with the fx group so it precedes the note-on.)

`synth.cpp` `fx()`:
```cpp
    case Fx::ARM: r.arm = val; break;
    ...
  if (cmd == kSynthArpChord) {  // before the Fx switch: not an Fx value
    r.arpN = chordNotes(60, val, p_.scaleRoot, static_cast<ScaleType>(p_.scaleType), r.arpNotes);
    for (int i = 0; i < r.arpN; ++i) r.arpNotes[i] -= 60;  // intervals
    return;
  }
```
New-note-step reset (`:160`, where `r.vib = r.arp = 0`): also `r.arm = kArmDefault; r.arpN = 0;`.

`control()` ARP block:
```cpp
  if (r.arp) {
    uint8_t offs[4] = {0, static_cast<uint8_t>(r.arp >> 4), static_cast<uint8_t>(r.arp & 15), 0};
    int n = 3;
    if (r.arpN > 1) { n = r.arpN; for (int i = 0; i < n; ++i) offs[i] = r.arpNotes[i]; }
    const int rate = (r.arm & 15) < 1 ? 1 : ((r.arm & 15) > kArmRateMax ? kArmRateMax : r.arm & 15);
    const int mode = (r.arm >> 4) & 3;
    v.arpT += static_cast<uint32_t>(dt);
    const uint32_t slot = static_cast<uint32_t>(stepSamples(v.track) / rate);
    const uint32_t k = slot ? v.arpT / slot : 0;
    int idx;
    switch (mode) {
      case 1: idx = (n - 1) - static_cast<int>(k % n); break;                           // DOWN
      case 2: { const int cyc = n > 1 ? 2 * n - 2 : 1; const int q = static_cast<int>(k % cyc);  // UPDOWN
                idx = q < n ? q : cyc - q; break; }
      case 3: idx = static_cast<int>(rnd() * n) % n; break;                             // RANDOM (per slot: cache k -> idx in v.arpK / v.arpIdx)
      default: idx = static_cast<int>(k % n); break;                                     // UP
    }
    pitch += offs[idx];
  }
```
RANDOM: add `uint32_t arpK = ~0u; uint8_t arpIdx = 0;` to `Voice`; recompute `arpIdx` only when `k != arpK`. Default `arm = 0x03`, no chord: `rate 3`, UP, offsets `0, x, y` → identical to today's thirds.

`arpOffset(v)` test hook: returns the offset last applied (store in `v.arpOff`).

**Step 4:** `pio test -e native -f test_expand`, `-f test_synth`, `-f test_sequencer` → PASS.

---

### Task 8: Velocity → cutoff / DECAY

**Files:** `lib/core/src/synth.cpp` (`controlFilter`, `macros()` / `:421` dec read), `test/test_synth/test_main.cpp`.

**Step 1: Failing tests** `test_velcut_moves_cutoff`: LP filter, cutoff 64, `velCut 32`, note vel 127 vs vel 64: `voice(v).flt` cutoff (add a `float cutoffHz() const` getter on `Svf` or compare the brightness: RMS of the rendered saw is higher at vel 127). Expected shift `32/64 × 63/64 × 6 ≈ 2.95` octaves. `test_velmac_shifts_decay`: FM Kick, `velMac 40`, DECAY 60: vel 127 rings longer than vel 64 (energy after 300 ms greater). `velCut == 0 && velMac == 0`: existing tests unchanged.

**Step 2:** → FAIL.

**Step 3: Implement** `controlFilter`, after the fenv term:
```cpp
  if (m.velCut) oct += m.velCut * (1.f / 64.f) * ((static_cast<int>(v.vel) - 64) * (1.f / 64.f)) * 6.f;
```
`macros()` and the direct `kMacDec` read (`:421`): after choosing the DECAY value,
```cpp
  if (m.velMac) dec = clampi(dec + m.velMac * (static_cast<int>(v.vel) - 64) / 64, 0, 127);
```
(`velMac` applies to FM / DRUM / SYNTH only — those are the callers of `macros()`.)

**Step 4:** `pio test -e native -f test_synth` → PASS.

---

### Task 9: File formats (project, presets, storage snapshot)

**Files:** `lib/core/src/inst_codec.cpp` (`packFm` / `unpackFm` bytes 10..13), `lib/core/src/preset_io.h` (`kPresetVersion = 4`), `lib/core/src/project_io.cpp` (`kAudiSize = 13`, `readAudi`, writer), `src/storage/storage.cpp:68` (copy the 7 new Project fields), tests `test/test_project_io`, `test/test_preset_io`.

**Step 1: Failing tests** (follow `test_samples_roundtrip` / the delay tests' pattern): round trip of `drive 77, rsend 12, velCut -20, velMac 33` and of the 7 Project fields; a 6-byte AUDI → defaults (`rvbSize 60 … scDepth 64`); AUDI values 200 / `scTrack 17` clamp (127 / 0); a FMIN record with bytes 10..13 = 0 → defaults; preset round trip; a preset with version 3 loads (`drive 0`); version 5 → `BadVersion`.

**Step 2:** → FAIL.

**Step 3: Implement**
```cpp
  // packFm, after b[9]:
  b[10] = m.drive; b[11] = m.rsend;
  b[12] = static_cast<uint8_t>(m.velCut); b[13] = static_cast<uint8_t>(m.velMac);
  // unpackFm:
  m.drive = clampu(b[10], 0, 127); m.rsend = clampu(b[11], 0, 127);
  m.velCut = clamps(static_cast<int8_t>(b[12]), -64, 63); m.velMac = clamps(static_cast<int8_t>(b[13]), -64, 63);
```
`project_io.cpp`: `kAudiSize = 13`; `readAudi` reads `min(size, 13)` bytes, applies fields 0..5 when `n >= 6` (as now) and 6..12 when `n >= 13`: `rvbSize = clampu(b[6]) … scTrack = b[11] <= kTracks ? b[11] : 0, scDepth = clampu(b[12])`; writer appends the 7 bytes. `storage.cpp`: copy the 7 fields in the snapshot.

**Step 4:** `pio test -e native -f test_project_io`, `-f test_preset_io`, `-f test_presets_factory` (factory presets still decode) → PASS.

---

### Task 10: UI

**Files:** `src/ui/inst_screen.h/.cpp`, `src/ui/proj_screen.h/.cpp`, `docs/manual.html`, `README.md`.

**Step 1: INST** (`inst_screen.h:39-54`): MAIN gets `kRsend = 8` after `kSend` (`kMainRows = 9`; ENV indices shift by one: `kAttack = 9 … kRelease = 12`, add `kVelCut = 13, kVelMac = 14, kCommon = 15`); every `kCommon`-relative constant follows. Tail: `kDrive = 0` first, `kFltMode = 1 … kKeytrack = 7, kLfoWave = 8 … kLfoDest = 11, kTailRows = 12, kFiltRows = 8`. Rows (`inst_screen.cpp`, same `Param` style as `Send`):
- `{"Rvb send", num(&Instrument::rsend), u7(&Instrument::rsend)}`
- `{"Drive", num(&Instrument::drive), u7(&Instrument::drive)}` (0 shows "OFF")
- `{"Vel>Cut", signed(&Instrument::velCut), s64(&Instrument::velCut), dim: fltMode == Off}`
- `{"Vel>Dec", signed(&Instrument::velMac), s64(&Instrument::velMac), dim: type is Chip || Sample}`
- LFO dest name tables (`:269-270`): append `"DRIVE"` to both; `lfoDestStep` already allows it.

**Step 2: PROJ** (`proj_screen.h:18`): `kRvbSize, kRvbDamp, kRvbLevel, kCompAmt, kCompRel, kScTrack, kScDepth` after `kDlyLevel`. Rows: `"Reverb"`, `"Rvb damp"`, `"Rvb level"` (u7); `"Comp"` (0 → "OFF"); `"Comp rel"` (format as ms: `20 * 50^(v/127)`); `"SC track"` (`0 → "OFF"`, else `T%d`; edit clamps 0..kTracks); `"SC depth"`. Check the list's visible-row count (`proj_screen.cpp:62` area) scrolls — it did for the delay rows.

**Step 3: Build** `pio run -e wt32`.

**Step 4: Docs** `docs/manual.html` (INST rows, PROJ rows, fx DRV / RVB / ARM incl. the ARP + CHD rule, sidechain how-to: SC track = the kick's track), `README.md` "Звук": one paragraph on drive, reverb, compressor / sidechain, ARP modes, velocity.

---

### Task 11: CPU bench

**Files:** `src/audio/audio.cpp` (`AUDIO_BENCH_FX` next to `AUDIO_BENCH_DRUM`), `docs/plans/2026-10-06-sound-fx-design.md` (CPU section).

**Step 1:** Under `#ifdef AUDIO_BENCH_FX`: reuse `benchDrumBegin()` (8 DRUM voices + filtered CHIP) and additionally set `drive = 100`, `rsend = 100` on every bench instrument, `project->rvbLevel = 100`, `compAmt = 100`, `scTrack = 1`. Build with `-DAUDIO_BENCH_FX`, flash (`pio run -e wt32 -t upload` — if the device is attached; otherwise leave this step for the user), read the status-bar `CPU %` after 10 s; repeat with `rvbLevel = 0` and `compAmt = 0`.

**Step 2:** Write the three numbers (baseline bench / + drive + reverb / + compressor) into the design doc's CPU section; if reverb exceeds 12 %, note it and propose halving comb lengths (size scale 0.5..1.0 → 0.35..0.7) as a follow-up, do not change the DSP here.

**Step 3:** Final: `pio test -e native` → every suite PASS; `pio run -e wt32` → compiles without the bench define.
