deemonoise/D-TRK/docs/plans/future-audio.md

# Планы на будущее: встроенный звук

Записано 2026-10-02. Все цифры по CPU — оценки, не замеры.

## Статус (2026-10-05)

**Вариант 1, этапы chiptune, сэмплер, FM, фильтр, 808/909 и пресеты — реализованы.** Решения и отличия от этого плана — в дизайне [2026-10-04-internal-audio-design.md](2026-10-04-internal-audio-design.md), план работ — [2026-10-04-internal-audio.md](2026-10-04-internal-audio.md), использование — README (раздел «Звук») и руководство.

Что сделано:
- вывод на встроенный усилитель NS4168 (разъём SPK, мост, моно), 32 кГц, блок 128 сэмплов; внешнего ЦАП нет;
- 16 инструментов CHIP / SAMPLE / FM, пул 16 голосов, MONO / POLY (до 4 на дорожку), ADSR, glide;
- CHIP: pulse (скважность, PWM-свип), triangle, saw, noise, metal, 16 wavetable в прошивке;
- SAMPLE: банк во flash (~9,9 МБ, 128 сэмплов), импорт WAV с SD, start / end / loop (fwd, ping-pong) / reverse, вид волны;
- выход дорожки MIDI / INT, fx SLD, VIB, ARP, VSL, OFS, CUT; PBN и PGM на INT-дорожках;
- загрузка `.wav` через Wi-Fi;
- FM: 8 машин в стиле Model:Cycles, макросы, p-lock, LFO (см. [дизайн](2026-10-05-fm-machines-design.md));
- фильтр на всех типах: SVF LP / BP / HP, своя огибающая (attack, decay), keytrack; fx `FLT`, `RES`; LFO на всех типах, новая цель CUTOFF (см. [дизайн](2026-10-05-filter-drum-presets-design.md));
- тип DRUM: 16 машин 808 / 909 (BD, SD, TOM, CP, RS, CL, CB, HH, CY), свои имена макросов, локи `DEC…CON`;
- пресеты инструментов: 32 заводских (CHIP, FM, DRUM) + свои на SD (`/presets/<ТИП>/…`, `.mti`), браузер с прослушиванием, раздел `/presets` в Wi-Fi.

По-прежнему в планах:
- virtual analog (PolyBLEP-осцилляторы; резонансный фильтр и LFO уже есть);
- эффекты: delay, reverb, send-шины;
- рисование wavetable на экране (сейчас 16 фиксированных таблиц);
- редактор сэмпла глубже (trim с записью в банк, нормализация);
- внешний ЦАП (PCM5102A) для линейного выхода; компенсация задержки INT (~14 мс) относительно MIDI;
- вариант 2 (отдельная синт-плата) — если понадобятся VA / reverb / длинные сэмплы; проработка на Teensy 4.1 + Audio Shield — [future-teensy.md](future-teensy.md).

Ниже — исходные заметки без изменений.

## Цель

Превратить MIDI-секвенсор в полноценный трекер со своим звуком: сэмплы, chiptune, FM, virtual analog, эффекты.

## Вариант 1: звук на самом ESP32-S3

Бюджет: при 44,1 кГц на одно ядро 240 МГц ≈ 5400 тактов на сэмпл. Ядро 0 (секвенсор лёгкий) можно отдать под звук, ядро 1 — UI.

| Движок | Тактов/голос | 8 голосов | Вывод |
|---|---|---|---|
| Chiptune (pulse/PWM, triangle, noise, wavetable) | 20–40 | ~5% | легко |
| Сэмплер (интерполяция, громкость, пан, огибающая) | 60–120 | ~15% | легко |
| FM 4-op | 150–250 | ~35% | нормально; 6-op (DX7) впритык |
| Virtual analog (2× PolyBLEP, резонансный фильтр, 2 огибающие, LFO) | 300–600 | 50–90% | впритык: 4–6 голосов, 32 кГц или простой SVF |
| Delay / reverb | ~50 / 1000+ | — | delay дёшев, reverb заметно ест |

Железо:
- ЦАП: модуль PCM5102A (~$3). На плате есть I2S-усилитель NS4168 (динамик) на GPIO 35/36/37 — ЦАП можно повесить параллельно на ту же шину. Пины сверить со схемой платы.
- Память сэмплов:
  - PSRAM 2 МБ, свободно ~1,3 МБ (~15 с моно 16 бит 44,1 кГц или ~30 с при 22 кГц);
  - flash 16 МБ, прошивка ~0,6 МБ — раздел ~10 МБ под банк сэмплов (~2 мин), чтение через кэш;
  - стриминг с SD — возможен, но сложнее и меньше голосов.
- Риск: кадр экрана в PSRAM гоняется на LCD, чтение сэмплов из PSRAM будет конкурировать. Сэмплы лучше держать во flash / внутренней RAM.

Архитектура:
- Аудио-задача: блоки 64–128 сэмплов (1,5–3 мс) в I2S через DMA.
- Секвенсор уже выдаёт события с метками времени и lookahead — внутренний синт становится ещё одним выходом рядом с MIDI. Каждая дорожка: внешний MIDI или внутренний инструмент. События раскладываются с точностью до сэмпла внутри блока.
- Новые трекерные fx: slide/portamento, vibrato, arpeggio, volume slide, sample offset, cut. Существующие RAT, GAT, CHD, NDG работают как есть.
- UI: вкладка INSTR (движок, параметры), браузер WAV на SD, редактор сэмпла (trim, loop, вид волны).
- Формат проекта: блок инструментов, сэмплы — ссылками на файлы на SD.
- Микшер: громкость/пан на дорожку, 1–2 send-шины эффектов.

Порядок:
1. Аудио-выход + chiptune — дёшево, проверяет весь путь (I2S, синхронизация, замер CPU).
2. Сэмплер.
3. FM 4-op.
4. VA — последним, ограниченная полифония.

## Вариант 2: отдельная синт-плата

Имеет смысл ради VA, reverb, длинных сэмплов и качества звука. Chiptune, сэмплер и FM потянет и сам S3.

Связь:
- Самое простое: синт-плата слушает существующий MIDI OUT (GPIO10) — трекер не меняется.
- Минус: 31250 бод ≈ 1 мс на ноту, аккорд из 8 нот размазывается на ~8 мс.
- Лучше: отдельный UART 1–2 Мбод со своим протоколом. Секвенсор шлёт события заранее (lookahead) с метками времени, синт ставит их точно в сэмпл.
- Сэмплы — на самой синт-плате (своя SD или flash), передавать по UART медленно.

Платы:

| Плата | Цена | Оценка |
|---|---|---|
| ESP8266 D1 mini (есть) | — | нет: одно ядро, нет FPU, слабый I2S, Wi-Fi рвёт тайминг. Максимум Wi-Fi-MIDI-мост |
| RP2040 (есть) | — | эксперименты: 2× M0+ 133 МГц (разгон ~250), 264 КБ RAM, I2S через PIO, нет FPU. Chiptune, сэмплер, простой FM — да; хороший VA — нет. Можно сразу подключить к MIDI OUT и поиграть |
| Raspberry Pi Pico 2 (RP2350) | ~$5 | 2× M33 150 МГц с FPU и DSP, 520 КБ RAM. FM и простой VA на 4–8 голосов |
| ESP32-S3 N16R8 devkit | ~$8 | та же среда, 8 МБ быстрой PSRAM, оба ядра под звук, код переносится из трекера |
| **Daisy Seed** | ~$30 | **рекомендация.** STM32H750 480 МГц, 64 МБ SDRAM, встроенный кодек 24 бит, DaisySP (VA, фильтры, reverb, delay) |
| Teensy 4.1 + Audio shield | ~$50 | 600 МГц, Audio library, готовый клон DX7 (MicroDexed) |

## Рекомендация

1. Начать звук на самом S3: PCM5102A + chiptune, затем сэмплер — всё внутри трекера, с общим проектом и вкладкой инструментов.
2. Если понадобятся VA / reverb / длинные сэмплы / чистый звук — Daisy Seed как модуль по быстрому UART с событиями с метками времени.
3. RP2040 — для быстрых экспериментов через MIDI OUT, в итоговую систему не брать.

## Перед стартом

- Дизайн (brainstorming): движки и такты на голос, частота дискретизации, хранение сэмплов, вкладка INSTR, протокол (если вторая плата).
- Первым шагом замерить реальную стоимость голоса на S3.
