deemonoise/D-TRK/docs/plans/2026-10-05-ui-tweaks.md

# UI Tweaks Implementation Plan

> **For Claude:** REQUIRED SUB-SKILL: Use superpowers:executing-plans to implement this plan task-by-task.

**Goal:** wrap-around list navigation, encoder selection in GRID, one Transpose... dialog, FX repeat on empty slots.

**Architecture:** see `2026-10-05-ui-tweaks-design.md`. Core gets `scaleDegrees()`; UI changes in `menu.cpp`,
`param_list.cpp`, `file_screen.cpp`, `grid_screen.*`, new `transpose_dialog.*` (copy of the EuclidDialog pattern).

**Tech Stack:** C++17, PlatformIO (esp32s3 + native Unity tests), LovyanGFX.

No commits (user rule).

---

### Task 1: `scaleDegrees()` in core
- Test `test/test_scale/test_main.cpp`: `test_scale_degrees` — Chromatic 12, Major 7, PentatonicMinor 5, Blues 6.
- Run `pio test -e native -f test_scale` — FAIL (undeclared).
- `lib/core/src/scale.h/.cpp`: `int scaleDegrees(ScaleType t) { return __builtin_popcount(scaleMask(t)); }`.
- Run again — PASS.

### Task 2: wrap-around
- `Menu::move`: index `(i + dir + count_) % count_`, loop at most `count_` times.
- `ParamList::onInput`: `sel_ = ((sel_ + delta) % count_ + count_) % count_`.
- `FileScreen` names list: wrap over `0..count_`; `sampleMove`: wrap over `kSwitchRow..sampleRowCount()-1`
  (skip-disabled rules unchanged).

### Task 3: encoder selection
- `GridScreen`: helper `selFollow()` — when `selOn_`, set `selT1_ = track()`, `selS1_ = curStep_` after
  `moveStep` / `moveTrack` / `moveField`.
- Menu id `kSelect`: `selOn_ = true`, anchor and end = cursor, toast "SELECT".
- EncClick (no shift) with `selOn_`: drop selection, no edit.
- `kCopySel` drops the selection after copying.

### Task 4: TransposeDialog
- New `src/ui/transpose_dialog.h/.cpp`: rows Amount, Mode, OK, Cancel; header buttons; Shift turn = octave
  (handled before ParamList so x10 is not applied); OK calls back with (amount, degrees).
- `GridScreen`: replace kTrUp1/kTrDn1/kTrUp12/kTrDn12 with `kTranspose`; dialog routed like euclid_;
  OK = `apply()` with pushUndo + `transposeSel`.

### Task 5: FX repeat
- `GridScreen::lastFx_[kTracks][2]`; `editTurn` FX / VAL on `cmd == None` with remembered cmd writes it;
  every FX / VAL edit with cmd != None stores the slot.

### Task 6: verify + docs
- `pio test -e native`, `pio run -e <board env>`; update `docs/manual.html` (GRID menu, selection, transpose, FX repeat, wrap).
