deemonoise/D-TRK/docs/plans/2026-10-05-bottom-tray-design.md

# Нижняя часть корпуса — корыто

Проблема: аккумулятор упирается в разъёмы на нижней стороне модуля (зазор 1,5 мм), крышка плохо садится.

Ограничение: верхнюю часть не менять — она уже собрана.

## Решение

- Низ — корыто: дно `lid_t` = 3 мм, стенки `wall` по периметру высотой `tray_h` = 4,5 мм, наружный профиль как у верха.
- Аккумулятор лежит на дне — на 4,5 мм ниже прежнего, зазор до модуля 6 мм.
- Угловые стойки на всю высоту корыта. Винты M3×10 DIN 912 (цилиндрическая голова под шестигранник) утоплены заподлицо: цековка ⌀6,2 × 3,2. Под головой 4,3 мм, винт входит в верх на 5,7 мм (гнездо вставки — 6).
  Корыто 3 мм не подходит: винт прошёл бы гнездо насквозь.
- Ложемент IP5306 выше на `tray_h`: гнездо Type-C остаётся напротив отверстия в верхе.
- Центрирующая губа по кромке: 1,2 × 1,5 мм, зазор 0,2 к внутренней стенке верха; вырезы у угловых стоек верха и у IP5306. Внутри корыта губа продолжается до дна и сливается со стенкой (не висит).
- Система координат верха не меняется: корыто строится вниз от z = `lid_t`, при `part="bottom"` поднимается на `tray_h`. Проверка — `case_top.stl` до и после правки побайтно совпадает.

Габарит по высоте +4,5 мм.
