deemonoise/D-TRK/docs/plans/2026-10-05-filter-drum-presets-design.md

# Фильтр, DRUM 808/909, пресеты — дизайн

Дата: 2026-10-05. Продолжение [FM-машин](2026-10-05-fm-machines-design.md) и пунктов «фильтр на все типы» и «машины 808/909» из [future-audio.md](future-audio.md). Все цифры по CPU — оценки до замера.

## Решения

| Вопрос | Решение |
|---|---|
| Фильтр | SVF (LP / BP / HP) + своя AD-огибающая + keytrack, на всех типах |
| Локи фильтра | fx `FLT` (cutoff) и `RES` |
| LFO | открыт всем типам; новая цель CUTOFF; макро-цели — только FM и DRUM |
| 808/909 | новый тип `DRUM`, свой движок «аналоговых» моделей, 16 машин |
| Макросы DRUM | те же 5 слотов и fx `DEC COL SHP SWP CON`, имена — под машину |
| Пресеты | заводские в прошивке (только чтение) + свои на SD |
| Папки | `/presets/<TYPE>/<CATEGORY…>/NAME.mti`, вложенность до 4, как `/samples` |
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
