deemonoise/D-TRK/src/engine/engine.h

#pragma once
#include <stdint.h>
#include "model.h"

namespace engine {

// SendProgram: arg = track. ReleaseTies: after the UI changed heard pattern data under a held TIE.
// ChainEdit: arg = (row << 8) | mt::ChainOp, after a write to Project.chain / chainLen / songMode.
// Post it while still holding lockProject(): the engine handles it before planning on the new chain.
// TrackOut: arg = track, after TrackCfg::out changed (post ReleaseTies first): ends its sounding notes.
// Fill: arg 1 = fill held, 0 = released. PerfOn: arg = track | mt::PerfFx << 8; PerfOff: arg = track.
enum class Cmd : uint8_t {
  StartStop, TogglePlay, Stop, QueuePattern, SelectPattern, SetBpm, SendProgram, ReleaseTies, ChainEdit, TrackOut,
  Fill, PerfOn, PerfOff
};

struct Command {
  Cmd cmd;
  uint16_t arg;
};

struct Status {
  bool playing;
  bool paused;
  uint8_t pattern;
  int8_t queued;
  uint8_t pos;
  uint32_t loop;
  int8_t songPos;  // chain index of the heard pattern, -1 outside song mode
  bool fill;       // fill held
  // The heard step: start (nowUs() time) and length, for stepPhase() (not compared: no redraws).
  uint64_t stepT;
  uint32_t stepUs;
  bool operator==(const Status& o) const {
    return playing == o.playing && paused == o.paused && pattern == o.pattern && queued == o.queued &&
           pos == o.pos && loop == o.loop && songPos == o.songPos && fill == o.fill;
  }
};

// First thing at boot: takes the sequencer's internal RAM before anything else can fragment it.
void reserve();
void begin(mt::Project* p);
bool seqInternal();  // the sequencer ended up in internal RAM
// False when the command queue was full (the command is lost).
bool post(Cmd c, uint16_t arg = 0);
// As post, waiting up to 50 ms for room: for commands that must not be lost (fill / perf release).
bool postWait(Cmd c, uint16_t arg = 0);
Status status();
// Tracks that sent a NoteOn since the last call (bit = track), for the activity LEDs.
uint16_t takeActivity();
// Engine timer time, us (time stamps of synth events).
uint64_t nowUs();
// Position inside the heard step of s now, 0..255 (live recording).
uint8_t stepPhase(const Status& s);

// Hold while writing project data from the UI. Keep it short: the engine waits on it.
void lockProject();
void unlockProject();

}  // namespace engine
